knivd/Configum1/graphics/3D-BOTTOM.JPG

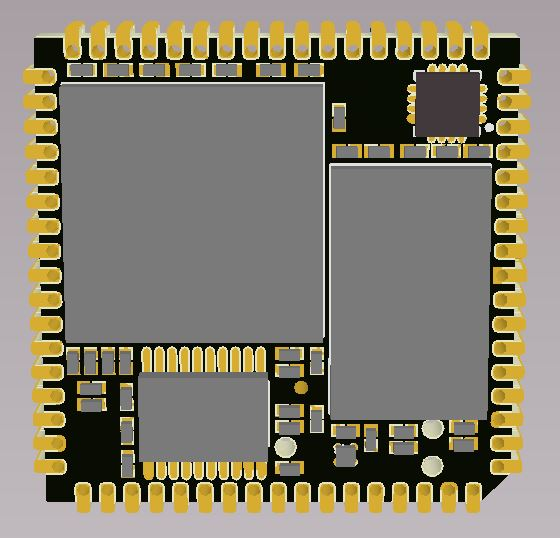
graphics/3D-BOTTOM.JPG
