knivd/Configum1/graphics/3D-TOP.JPG

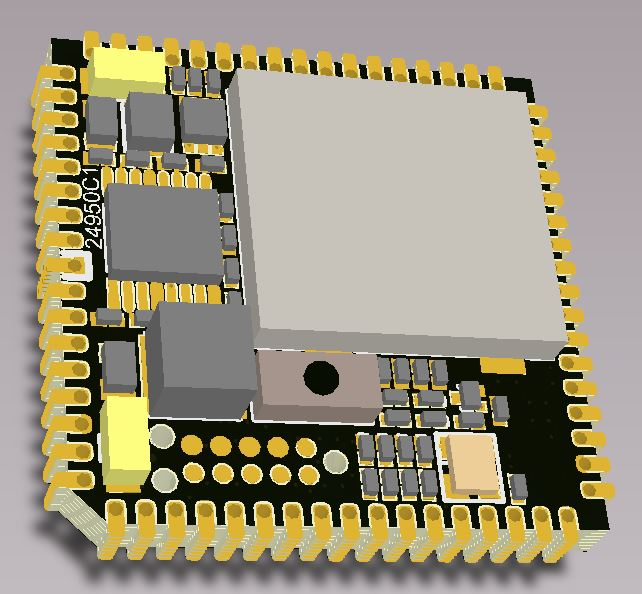
graphics/3D-TOP.JPG
