knivd/Configum1/graphics/DTX2-4950C.jpg

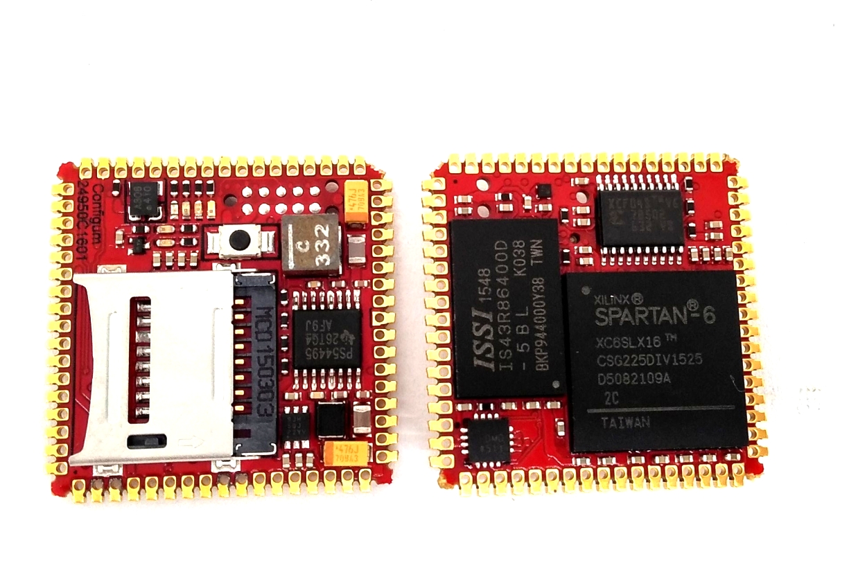
graphics/DTX2-4950C.jpg
