knivd/Configum1/docs/Spartan 6/Examples/BPC3010_Papilio_Pro.pdf

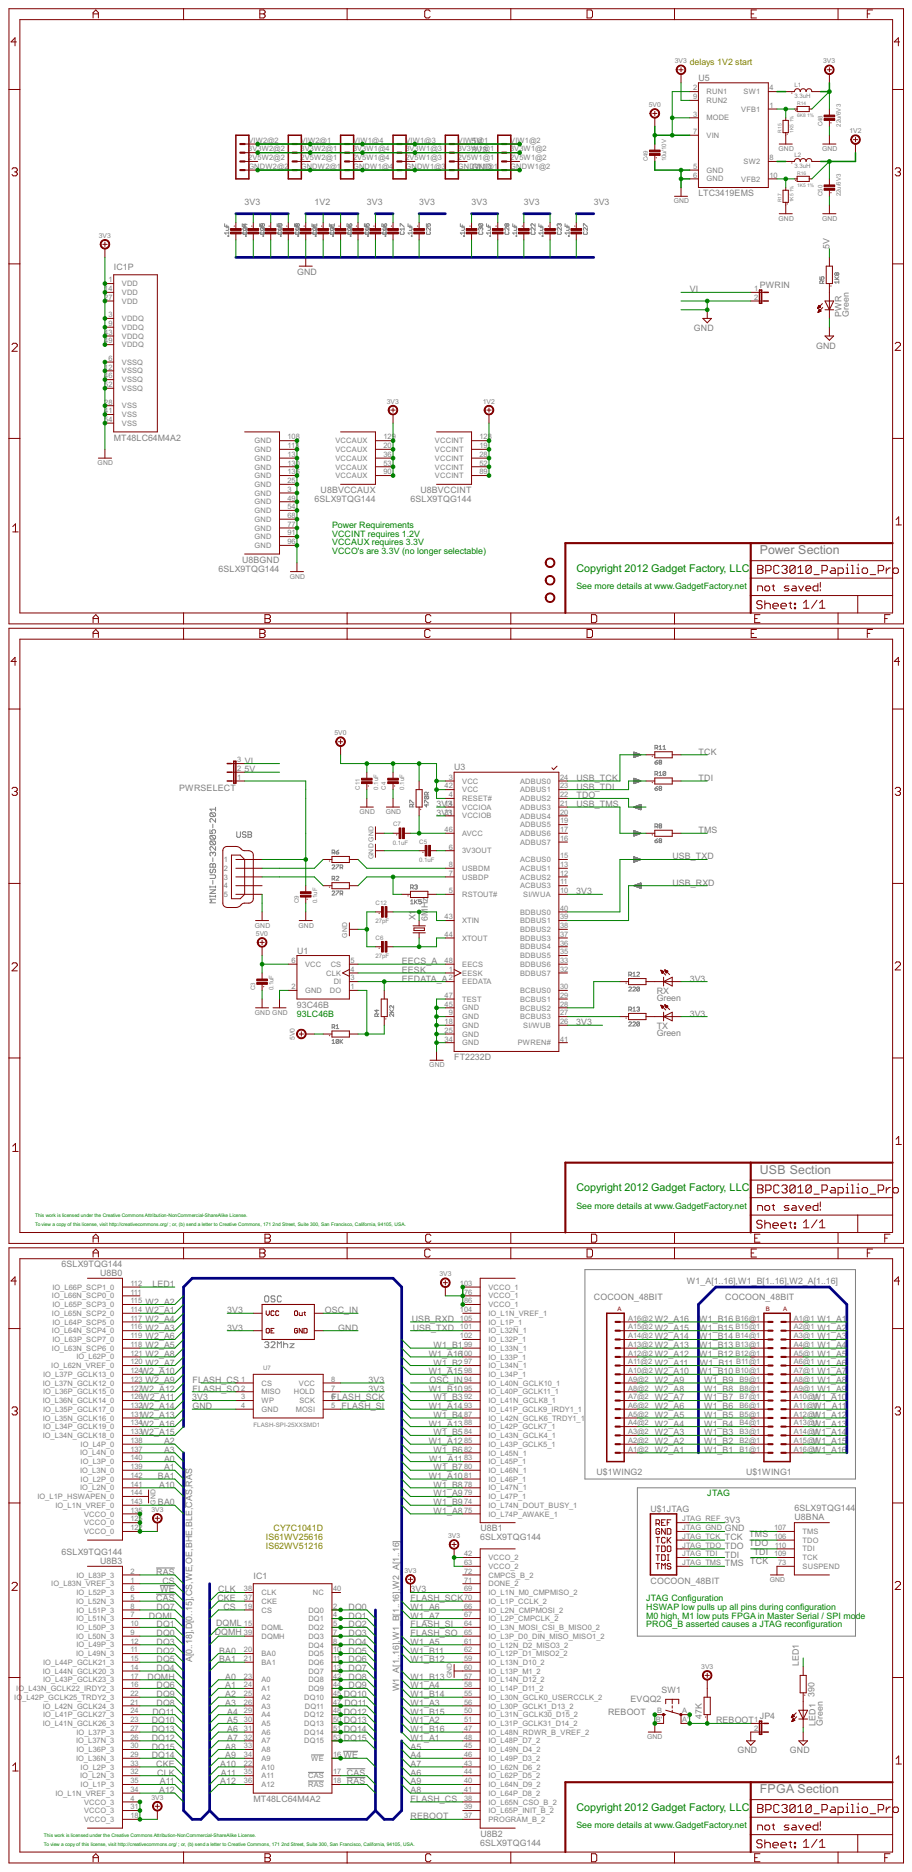
[picture p12: page 1]

3V3W2@2 VIW2@2 GNDW2@2 | 3V3W2@1 VIW2@1 GNDW2@1 | 3V3W1@4 VIW1@4 GNDW1@4 | 3V3W1@3 VIW1@3 GNDW1@3 | 3V3W1@1 VIW1@1 GNDW1@1 3V3

2V5W2@2 | 2V5W2@1 | 2V5W1@4 | 2V5W1@3 | 2V5W1@1 GND

Power Requirements VCCINT requires 1.2V

VCCAUX requires 3.3V
VCCO's are 3.3V (no longer selectable)

Copyright 2012 Gadget Factory, LLC

See more details at www.GadgetFactory.net

A[0..18],D[0..15],CS,WE,OE,BHE,BLE,CAS,RAS

JTAG Configuration HSWAP low pulls up all pins during configuration M0 high, M1 low puts FPGA in Master Serial / SPI mode PROG_B asserted causes a JTAG reconfiguration

This work is licensed under the Creative Commons Attribution-NonCommercial-ShareAlike License. To view a copy of this license, visit http://creativecommons.org/ ; or, (b) send a letter to Creative Commons, 171 2nd Street, Suite 300, San Francisco, California, 94105, USA.
