knivd/Configum1/docs/Spartan 6/Examples/SCH-TE0600-02.pdf

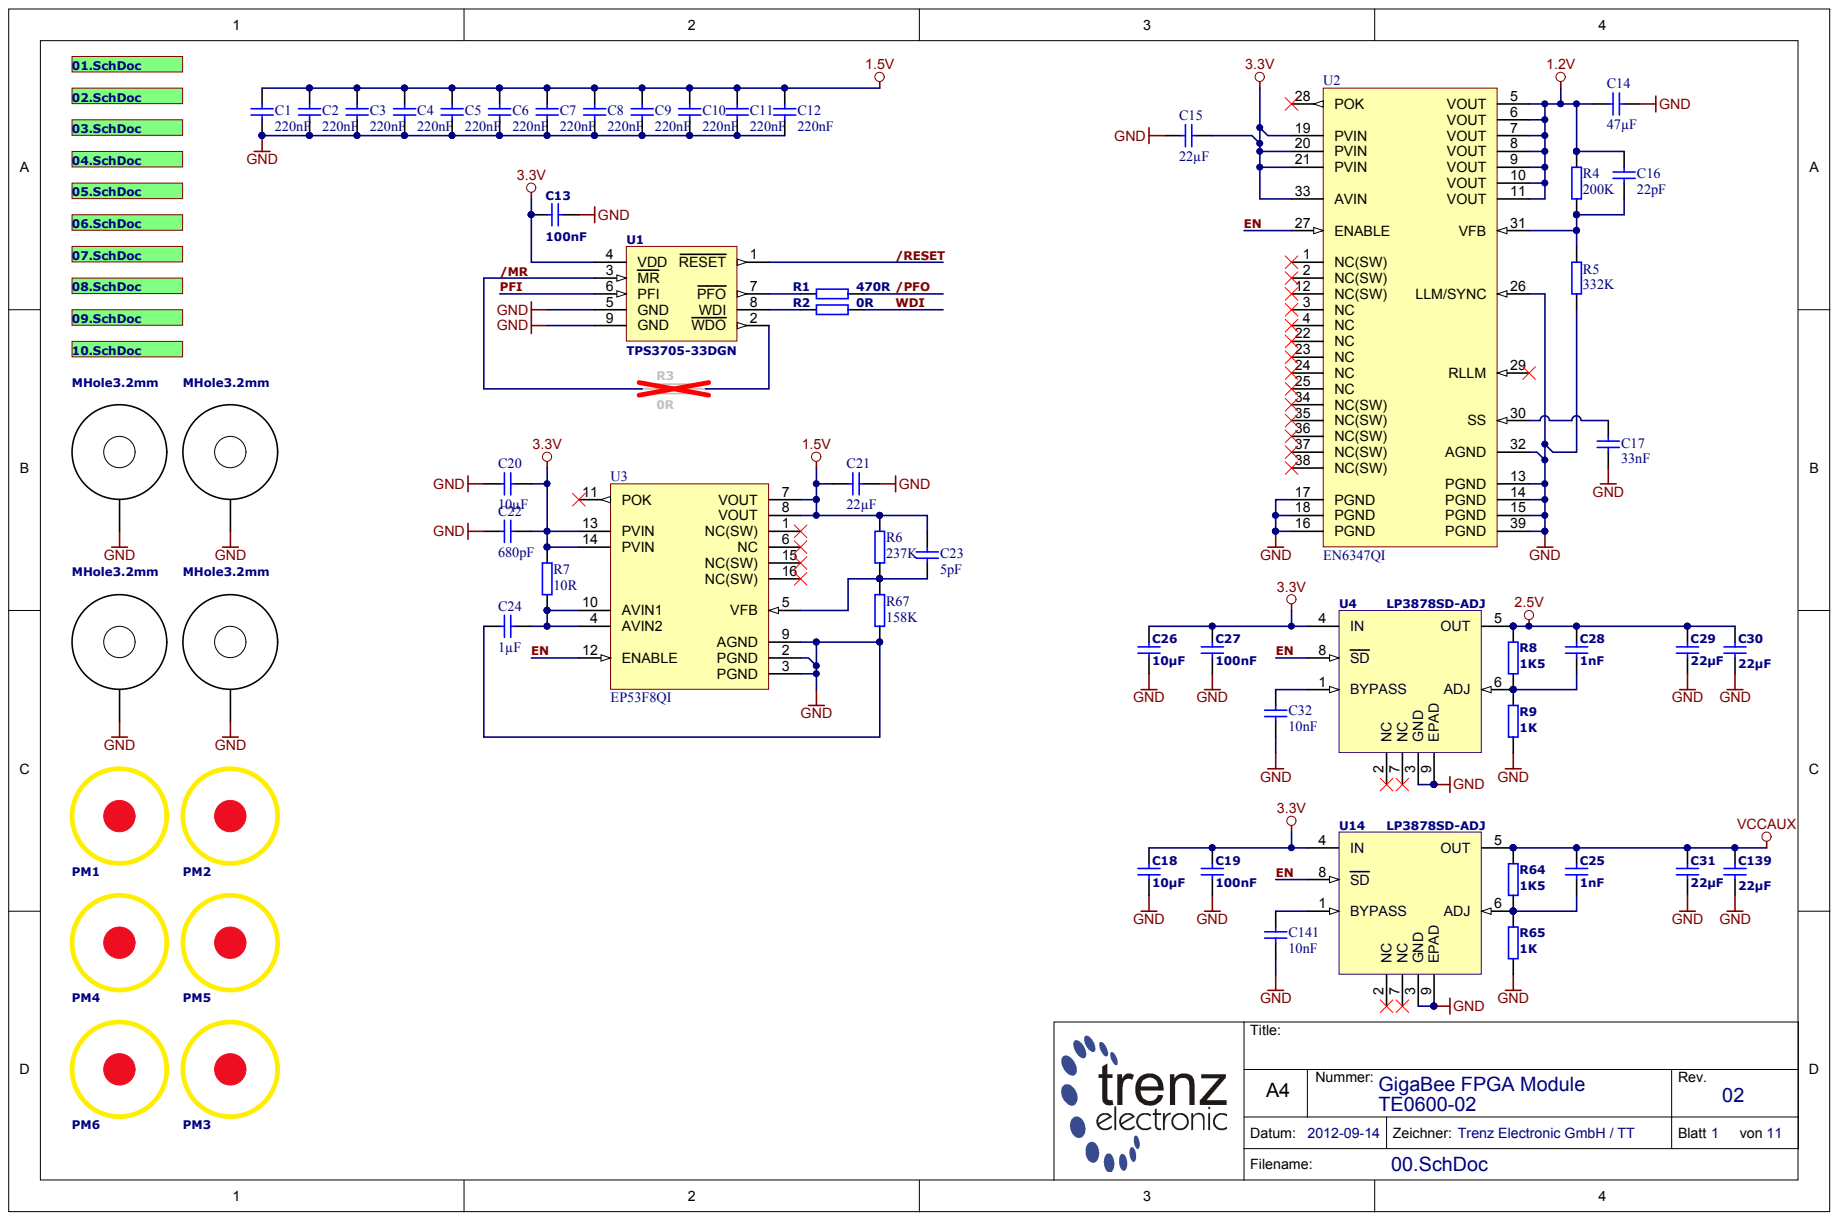
[picture p13: page 1]

Title:

A4 | Nummer: GigaBee FPGA Module | Rev. 02

Datum: | Zeichner: Trenz Electronic GmbH / TT | Blatt 1 von 11

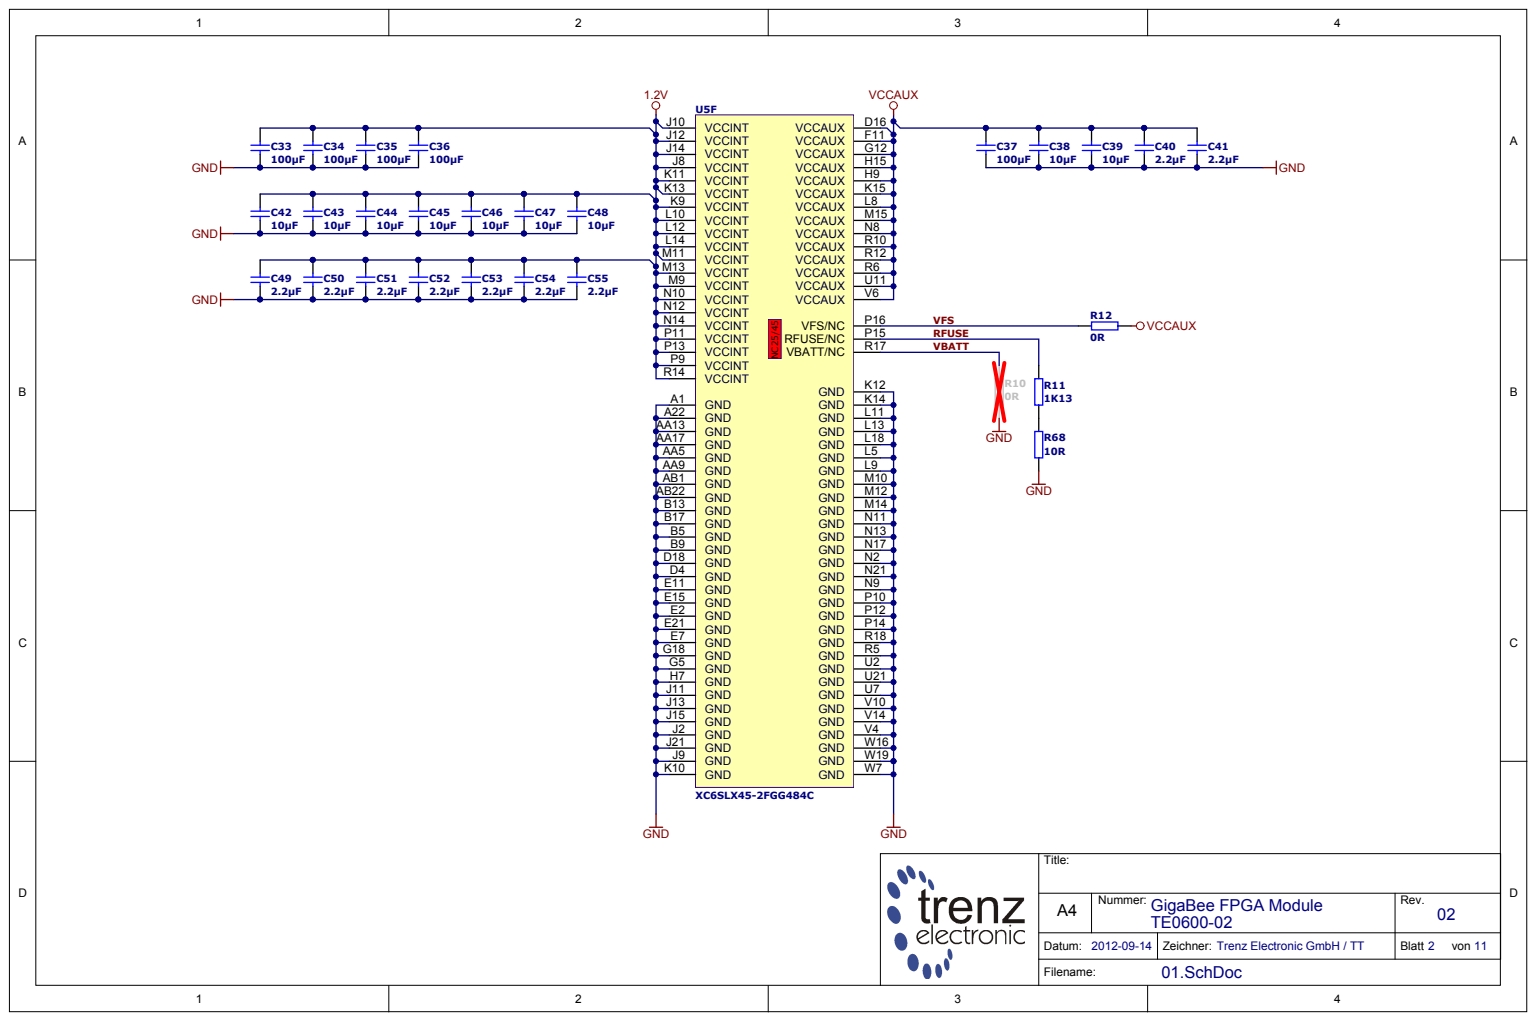
[picture p14: page 2]

VCCINT J14
VCCINT J8
VCCINT K11
VCCINT K13

VCCINT L10
VCCINT L12
VCCINT L14
VCCINT M11

VCCINT M9
VCCINT N10
VCCINT N12
VCCINT N14
VCCINT P11

GND A22
GND AA13
GND AA17
GND AA5
GND AA9
GND AB1
GND AB22
GND B13
GND B17
GND B5
GND B9
GND D18
GND D4
GND E11
GND E15
GND E2
GND E21
GND E7
GND G18
GND G5
GND H7
GND J11
GND J13
GND J15
GND J2
GND J21
GND J9

Title:

A4 | Nummer: GigaBee FPGA Module | Rev. 02

Datum: | Zeichner: Trenz Electronic GmbH / TT | Blatt 2 von 11

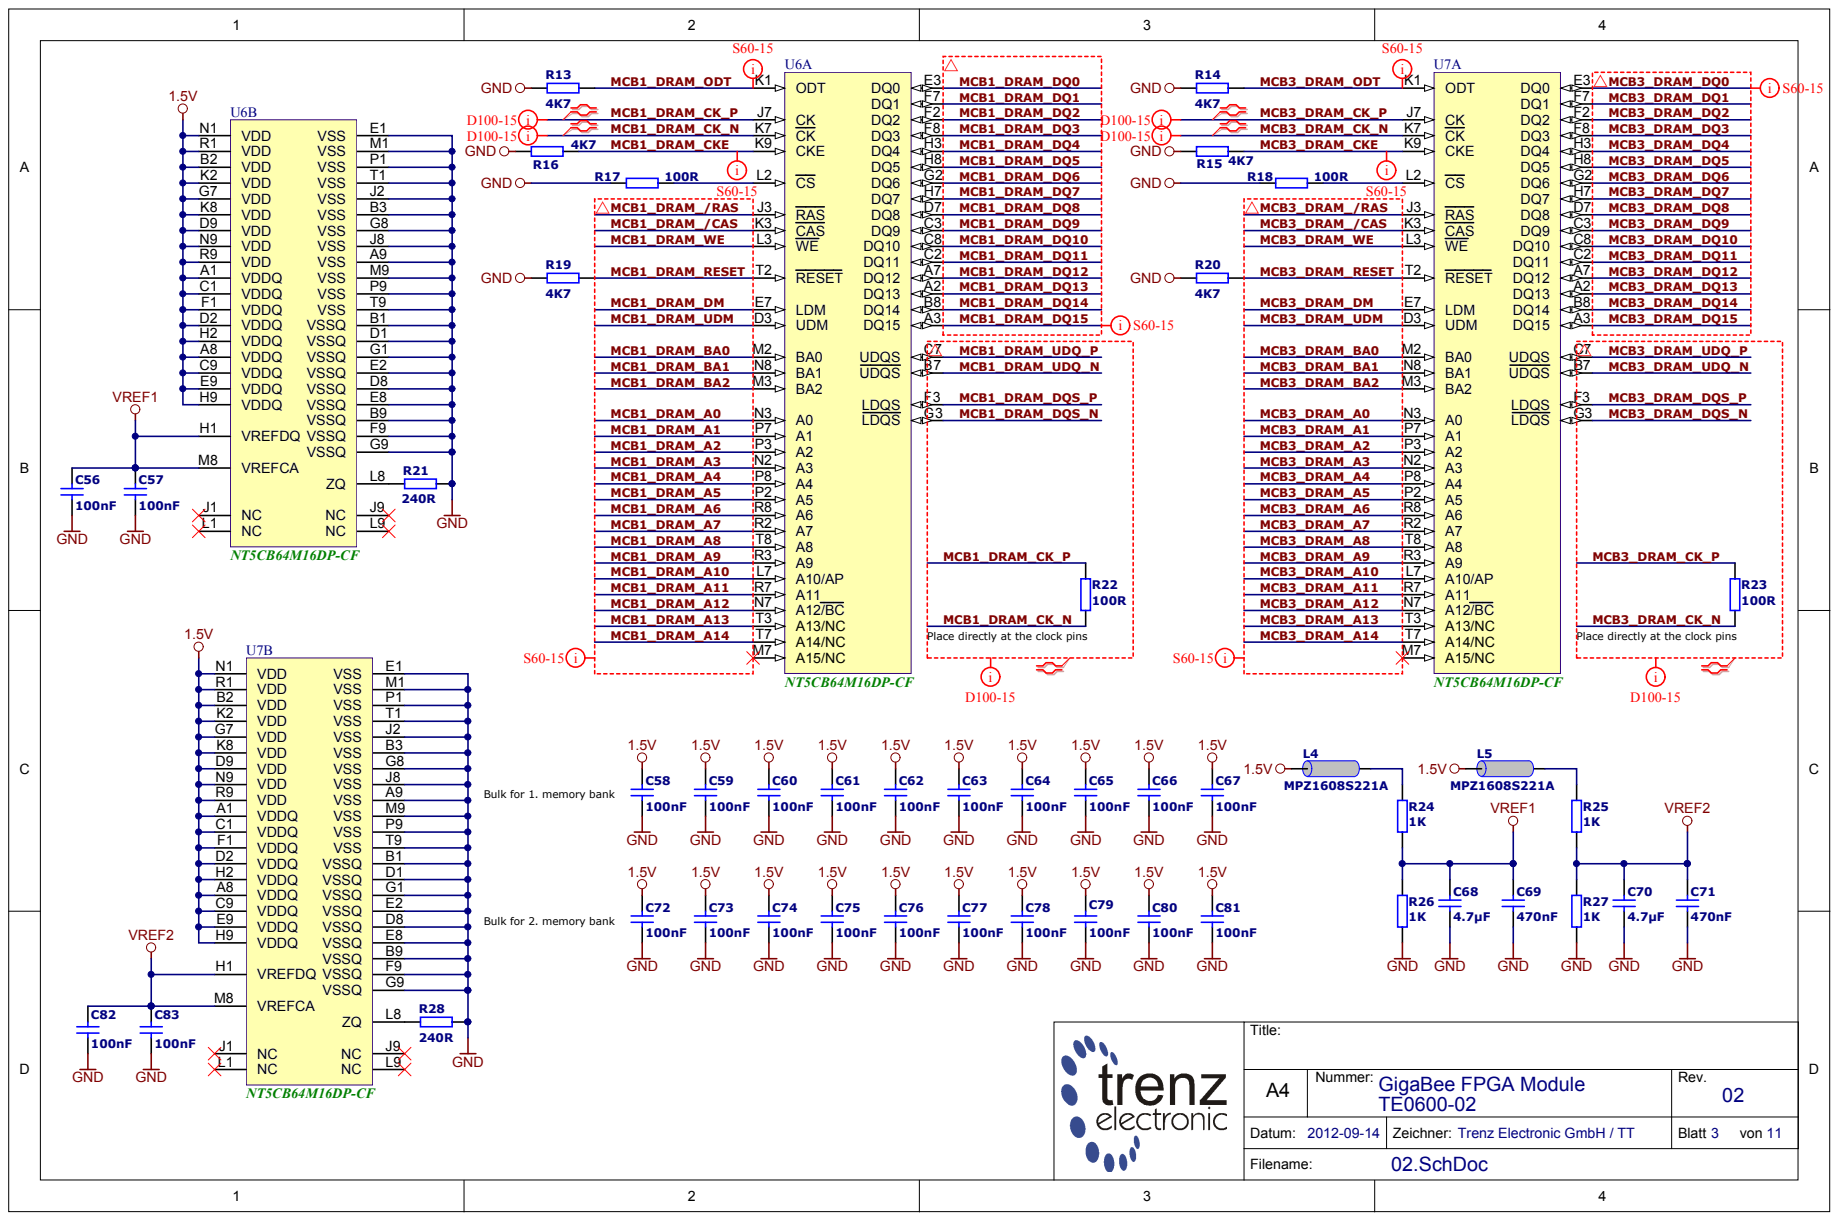
[picture p15: page 3]

VDD R1
VDD B2
VDD K2
VDD G7
VDD K8
VDD D9
VDD N9
VDD R9

Bulk for 1. memory bank

VDDQ A1
VDDQ C1
VDDQ F1
VDDQ D2
VDDQ H2
VDDQ A8
VDDQ C9

Bulk for 2. memory bank

Title:

A4 | Nummer: GigaBee FPGA Module TE0600-02 | Rev. 02

Datum: 2012-09-14 | Zeichner: Trenz Electronic GmbH / TT | Blatt 3 von 11

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
D | D
C | C
B | B
A | A
| Title:
A4 | Nummer: GigaBee FPGA Module TE0600-02 | Rev. 02
Datum: 2012-09-14 | Zeichner: Trenz Electronic GmbH / TT | Blatt 4 von 11
Filename: | 03.SchDoc

Trace widths should be 3 to 5 mils.
? | Trace spacing should be three times the trace width.
? | Signals must not be routed over splits or voids.
? | Routing of differential pairs adjacent to noisy signal lines or high-speed
switching
devices such as clock chips should be avoided.
? The spacing between differential clocks/strobes and other signals on the same PCB
layer should be 20 mil. The 20 mil spacing should be maintained when using serpentine routing for length matching.
Differential clocks/strobes are to be routed as 100O differential signals. The clock
pairs must be routed on the same PCB layer with no layer changes or hops after the
initial pad to via breakout.
The Data (DQ), Data Mask (DM), and Data Strobe (DQS) signals should receive the highest
priority (that is, routed first), because they are the highest speed DDR signals. ? DQ, DM, and DQS signals should be routed in a data group (per byte). Each group should have similar loading and routing to maintain timing and signal integrity. ? The provided spacing should be 20 mil between a data group and any other signals.
? | DQS signals should be isolated from other signals by 20 mil to avoid crosstalk.
? | There should be a maximum of ±25 ps electrical delay (±150 mil) between any
DQ/DM and its associated DQS strobe.
? | A data group should be referenced to a GROUND plane.
? | DQ bit swapping at the memory interface is permitted to facilitate layout.
Swapping
should only be done within a data group.
? | DQS to DQS_N trace lengths should be matched (±10 mil).
? | Memory terminations (if external terminations are used) should be placed after
the
associated memory component in a fly-by fashion.
? For 16-bit DDR devices, the LDQS/LDQS_N and UDQS/UDQS_N trace lengths
should be matched within ±25 ps of the electrical delay (±150 mil).
When the data groups have been routed, the next highest priority is the differential clock
(CK / CK_N). The clock should be routed first because all address and control trace length
matching must be referenced to the differential clock PCB trace length, which might need
to be adjusted as the layout task proceeds.
? | CK to CK_N trace lengths must be matched (±10 mil).
? | CK and DQS trace lengths must be matched (±250 mil) to maximize setup and hold
margins.
? There must be a maximum ±50 ps electrical delay (±300 mil) between any address/control signals and the associated CK and CK_N differential clock FPGA output.
? Address and control signals can be referenced to a POWER plane if a GROUND plane
is not next to this group of signals in the PCB stack-up.
To avoid crosstalk, address and command signals should be kept on a different routing layer from DQ, DQS, and DM.
? Differential clock terminations (if external terminations are used) must be located as
close as possible to the load, after the clock pads of the PCB. PCB trace lengths used in
trace length matching must exclude the CLINE length of the PCB trace from memory ball to terminating resistor.

Classnames:
S60-15 uses 1.5V or GND plane as reference D100-15 uses 1.5V or GND plane as reference

S60-25 uses 2.5V or GND plane as reference D100-25 uses 2.5V or GND plane as reference

S60-IO uses VCCIO0 or GND plane as reference D100-IO uses VCCIO0 or GND plane as reference

S60-33 uses 3.3V or GND plane as reference D100-33 uses 3.3V or GND plane as reference

R74 | 0R
R76 | 0R
R77 | 0R
GND R78 | 0R

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
Board Revisions

Assembly Variants

Enable pullups in FPGA

AV0 = 0 -> commercial AV0 = 1 -> Industrial

AV3 AV2 AV1
0 | 0 | 0 | 2 x 128 MBit, speedgrade 2
0 | 0 | 1 | 2 x 128 MBit, speedgrade 3
0 | 1 | 0 | 2 x 512 MBit, speedgrade 3

BR3 BR2 BR1 BR0
1 | 1 | 1 | 1 | -01 Initial revision
1 | 1 | 1 | 0 | -02 | GND

### NetTie1

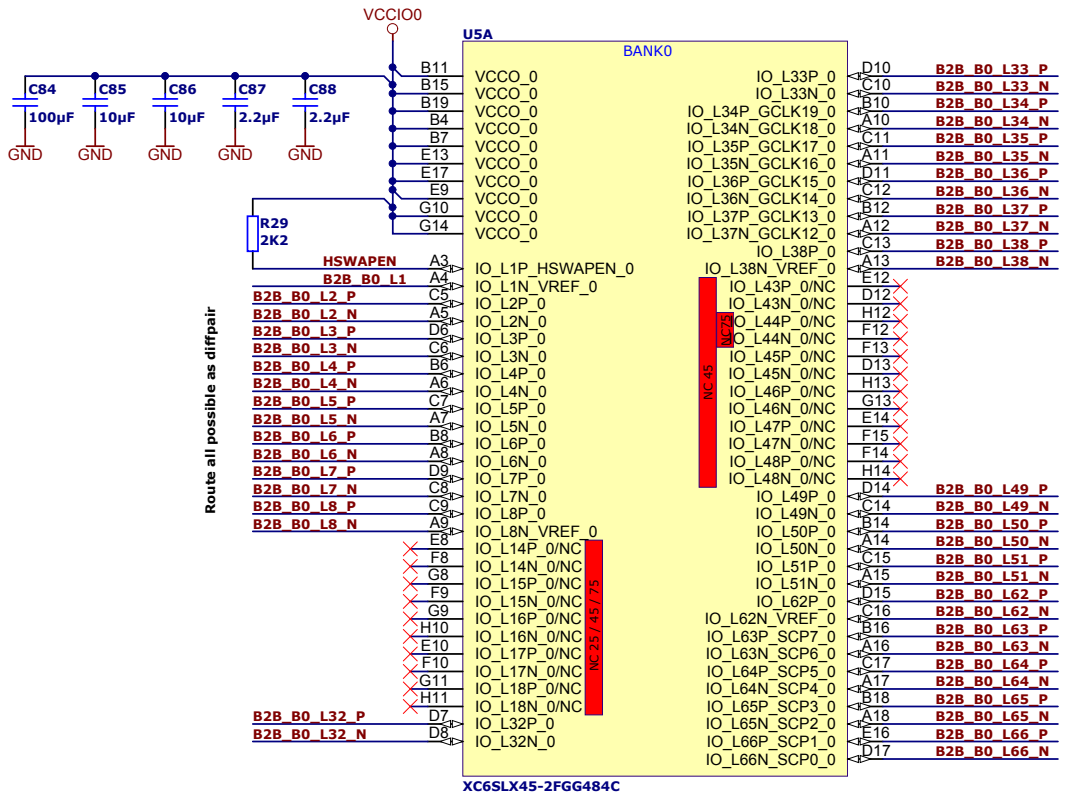
[picture p16: page 5]

VCCO_0 B19
VCCO_0 B4
VCCO_0 B7
VCCO_0 E13
VCCO_0 E17

Title:

A4 | Nummer: GigaBee FPGA Module | Rev. 02

Datum: | Zeichner: Trenz Electronic GmbH / TT | Blatt 5 von 11

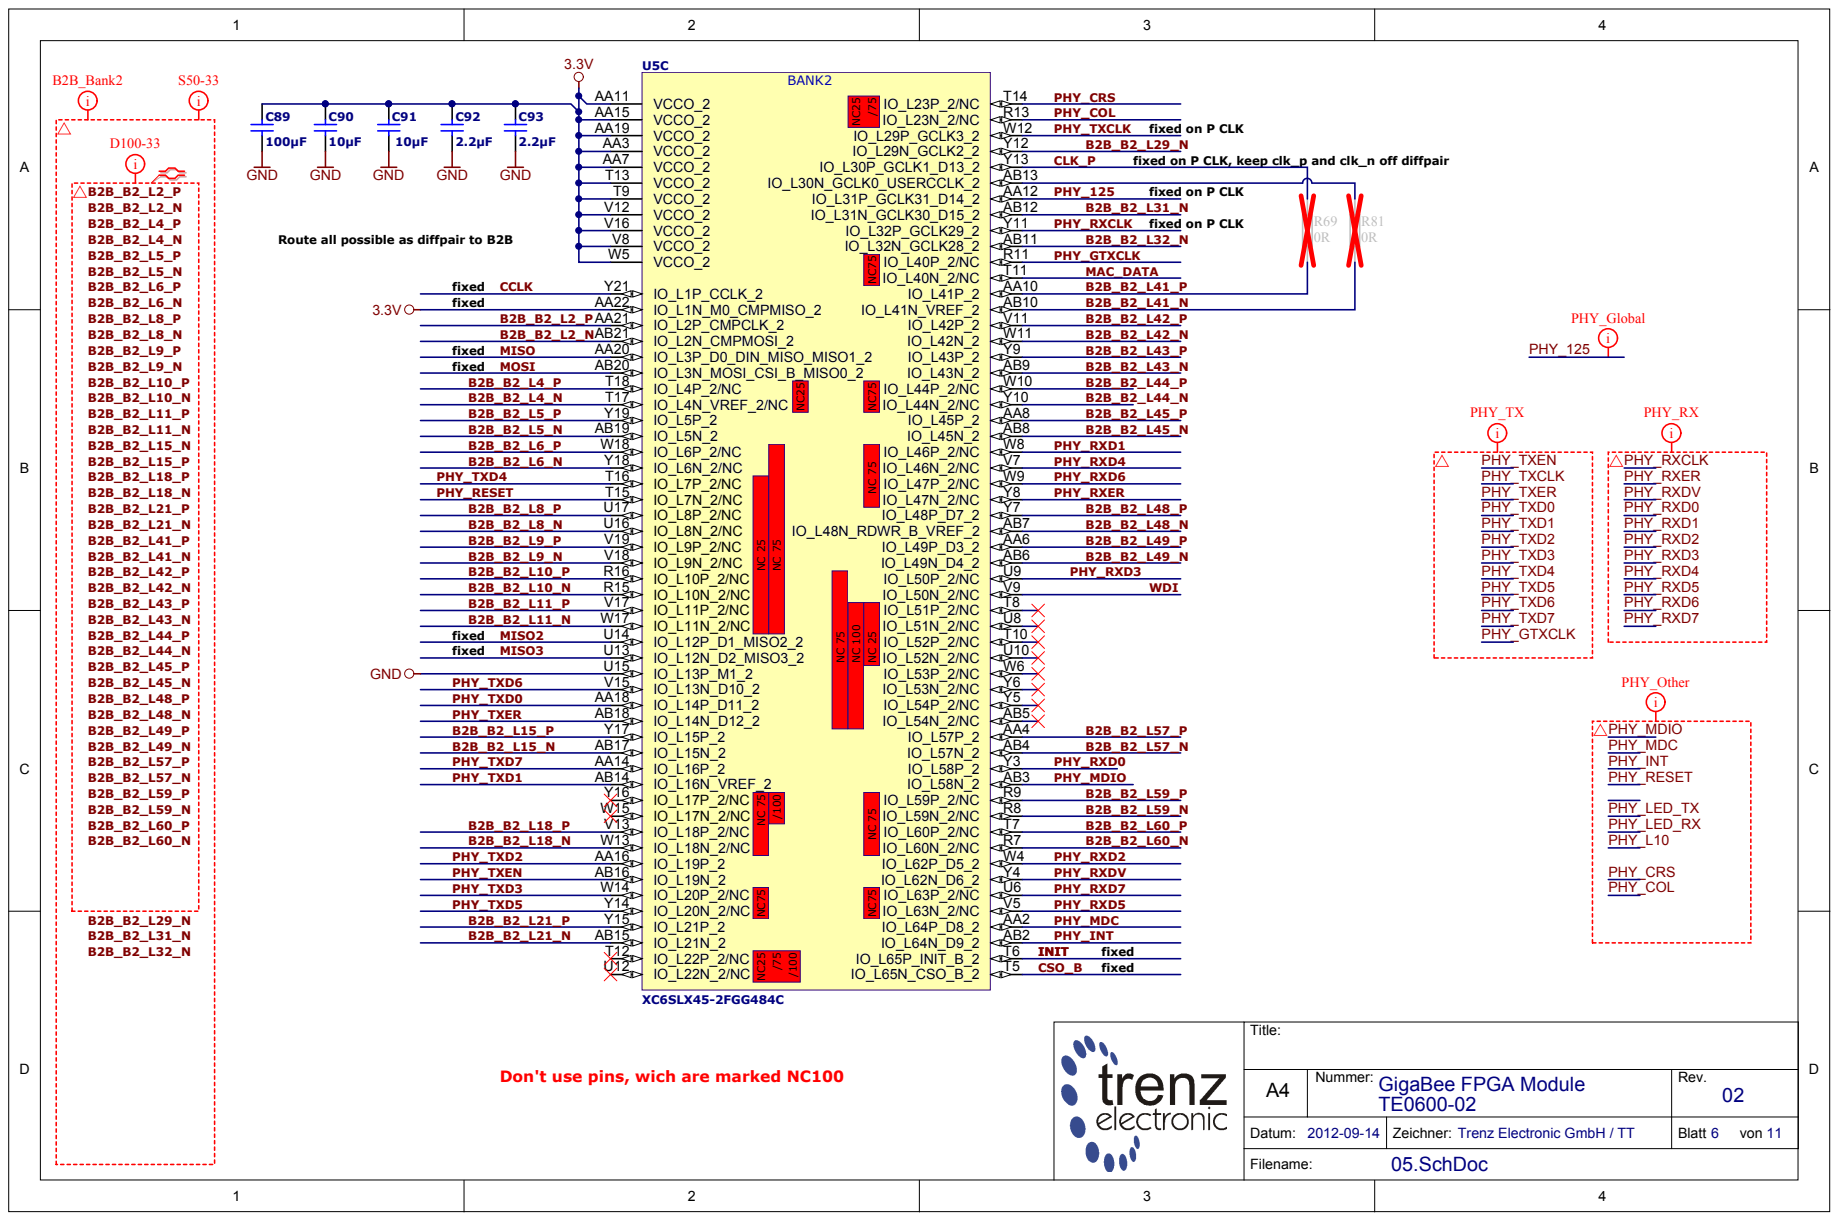
[picture p17: page 6]

VCCO_2 AA3
VCCO_2 AA7

K, keep clk_p and clk_n off diffpair

VCCO_2 T9 | PHY_125 fixed on P C L K
VCCO_2 V12
VCCO_2 V16
VCCO_2 V8

sible as diffpair to B2B

Title:

Don't use pins, wich are marked NC100

A4 | Nummer: GigaBee FPGA Module | Rev. 02

Datum: | Zeichner: Trenz Electronic GmbH / TT | Blatt 6 von 11

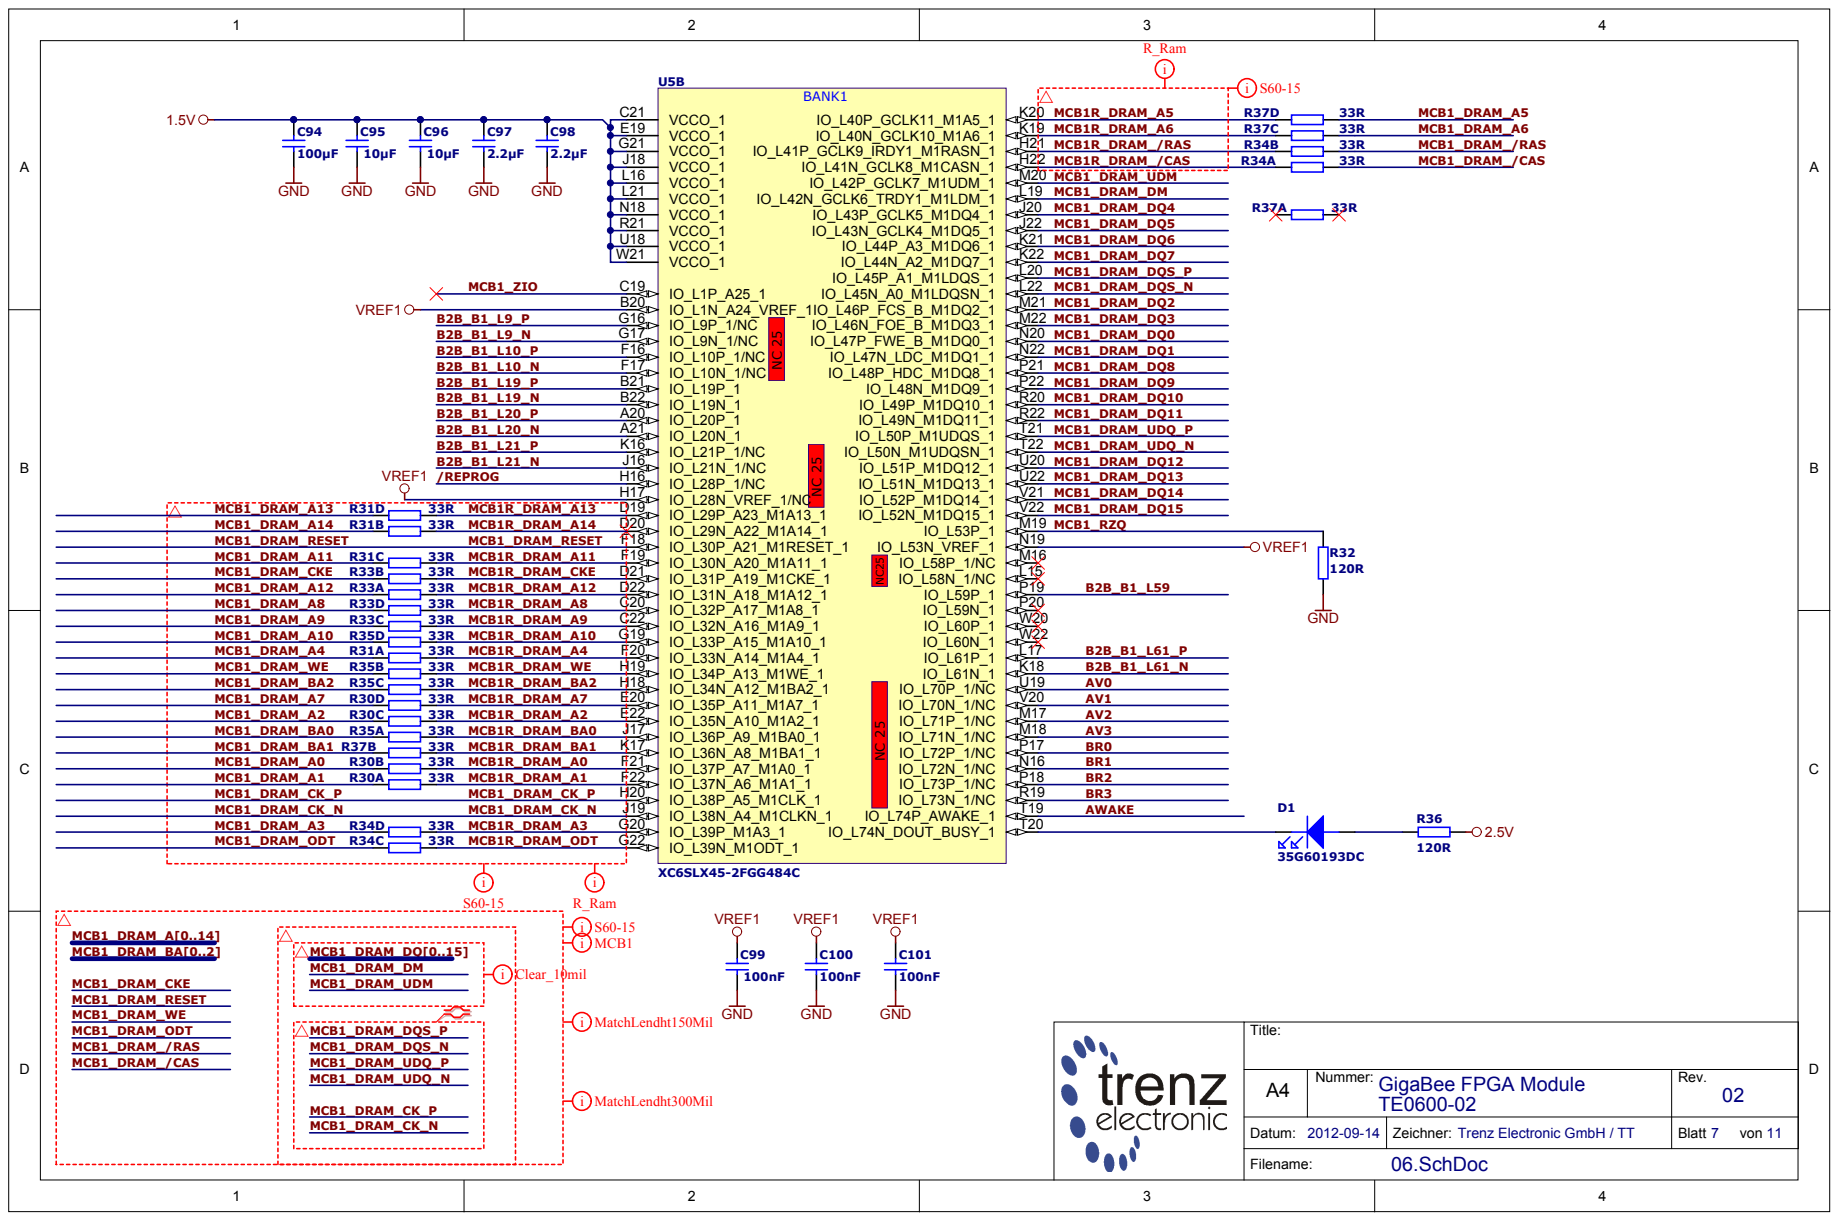
[picture p18: page 7]

VCCO_1 E19 | M CB1R_DRAM_A6
VCCO_1 G21 | M CB1R_DRAM_/RAS
VCCO_1 J18 | M CB1R_DRAM_/CAS
VCCO_1 L16
VCCO_1 L21
VCCO_1 N18
VCCO_1 R21
VCCO_1 U18

M CB1_DRAM_RESE T | IO_L30P_A21_M1RESET_1 F18

M CB1_DRAM_C K_P | IO_L38P_A5_M1CLK_1 H20
M CB1_DRAM_C K_N | IO_L38N_A4_M1CLKN_1 J19

A4 | Nummer: GigaBee FPGA Module | Rev. 02

Datum: | Zeichner: Trenz Electronic GmbH / TT | Blatt 7 von 11

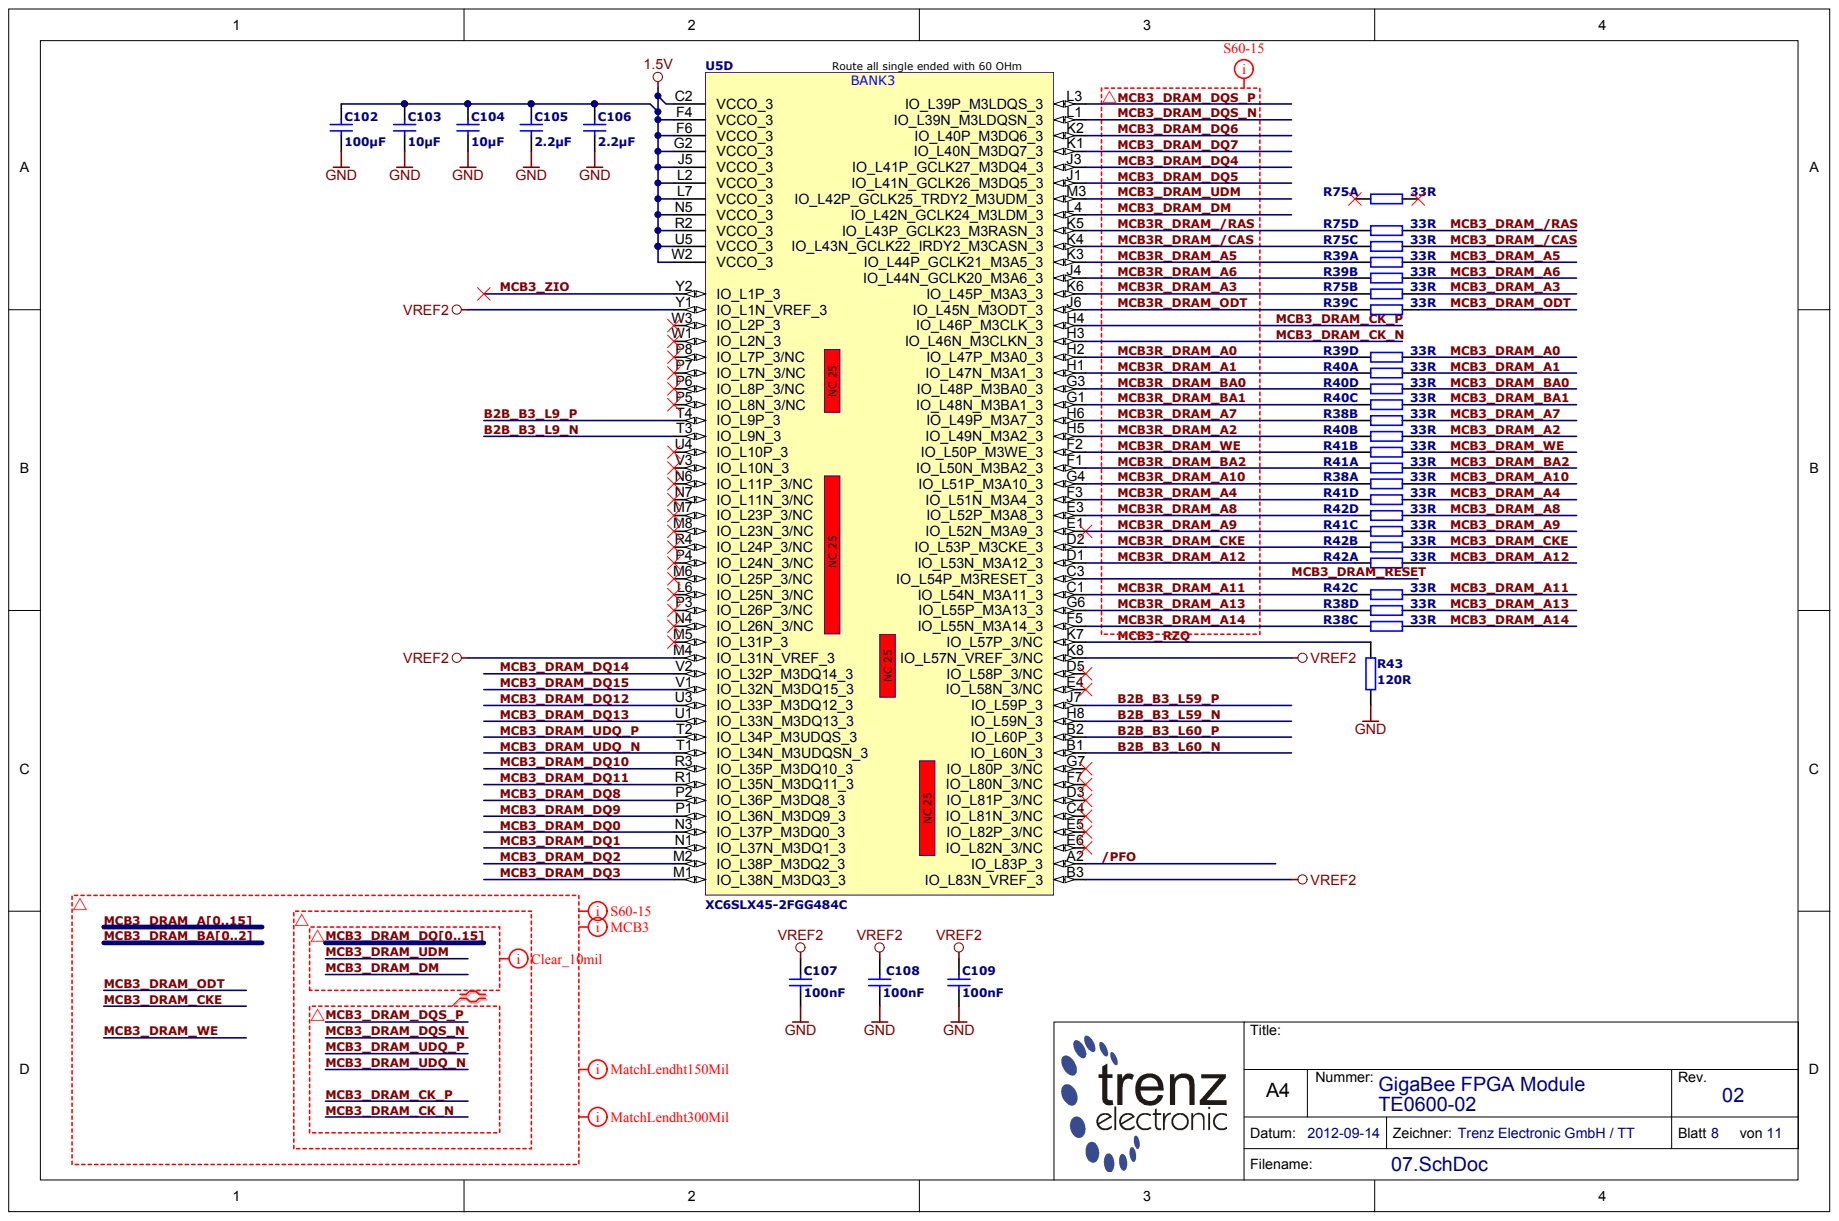
[picture p19: page 8]

Route all single ended with 6
BANK3

VCCO_3 F6
VCCO_3 G2
VCCO_3 J5
VCCO_3 L2
VCCO_3 L7
VCCO_3 N5
VCCO_3 R2
VCCO_3 U5 | M CB3R_DRAM_/CAS
VCCO_3 W2 | M CB3R_DRAM_A5
IO_L1P_3 Y2 IO_L1N_VREF_3 Y1 | M CB3R_DRAM_A6

M CB3R_DRAM_A3
M CB3R_DRAM_ODT

IO_L2P_3 W3 | M CB3R_DRAM_A0

IO_L9P_3 T4 IO_L9N_3 T3 IO_L10P_3 U4 | M CB3R_DRAM_A7

M CB3R_DRAM_A2
M CB3R_DRAM_W E

IO_L10N_3 V3 | M CB3R_DRAM_BA2
IO_L11P_3/NC N6 | M CB3R_DRAM_A10

Title:

A4 | Nummer: GigaBee FPGA Module | Rev. 02

Datum: | Zeichner: Trenz Electronic GmbH / TT | Blatt 8 von 11

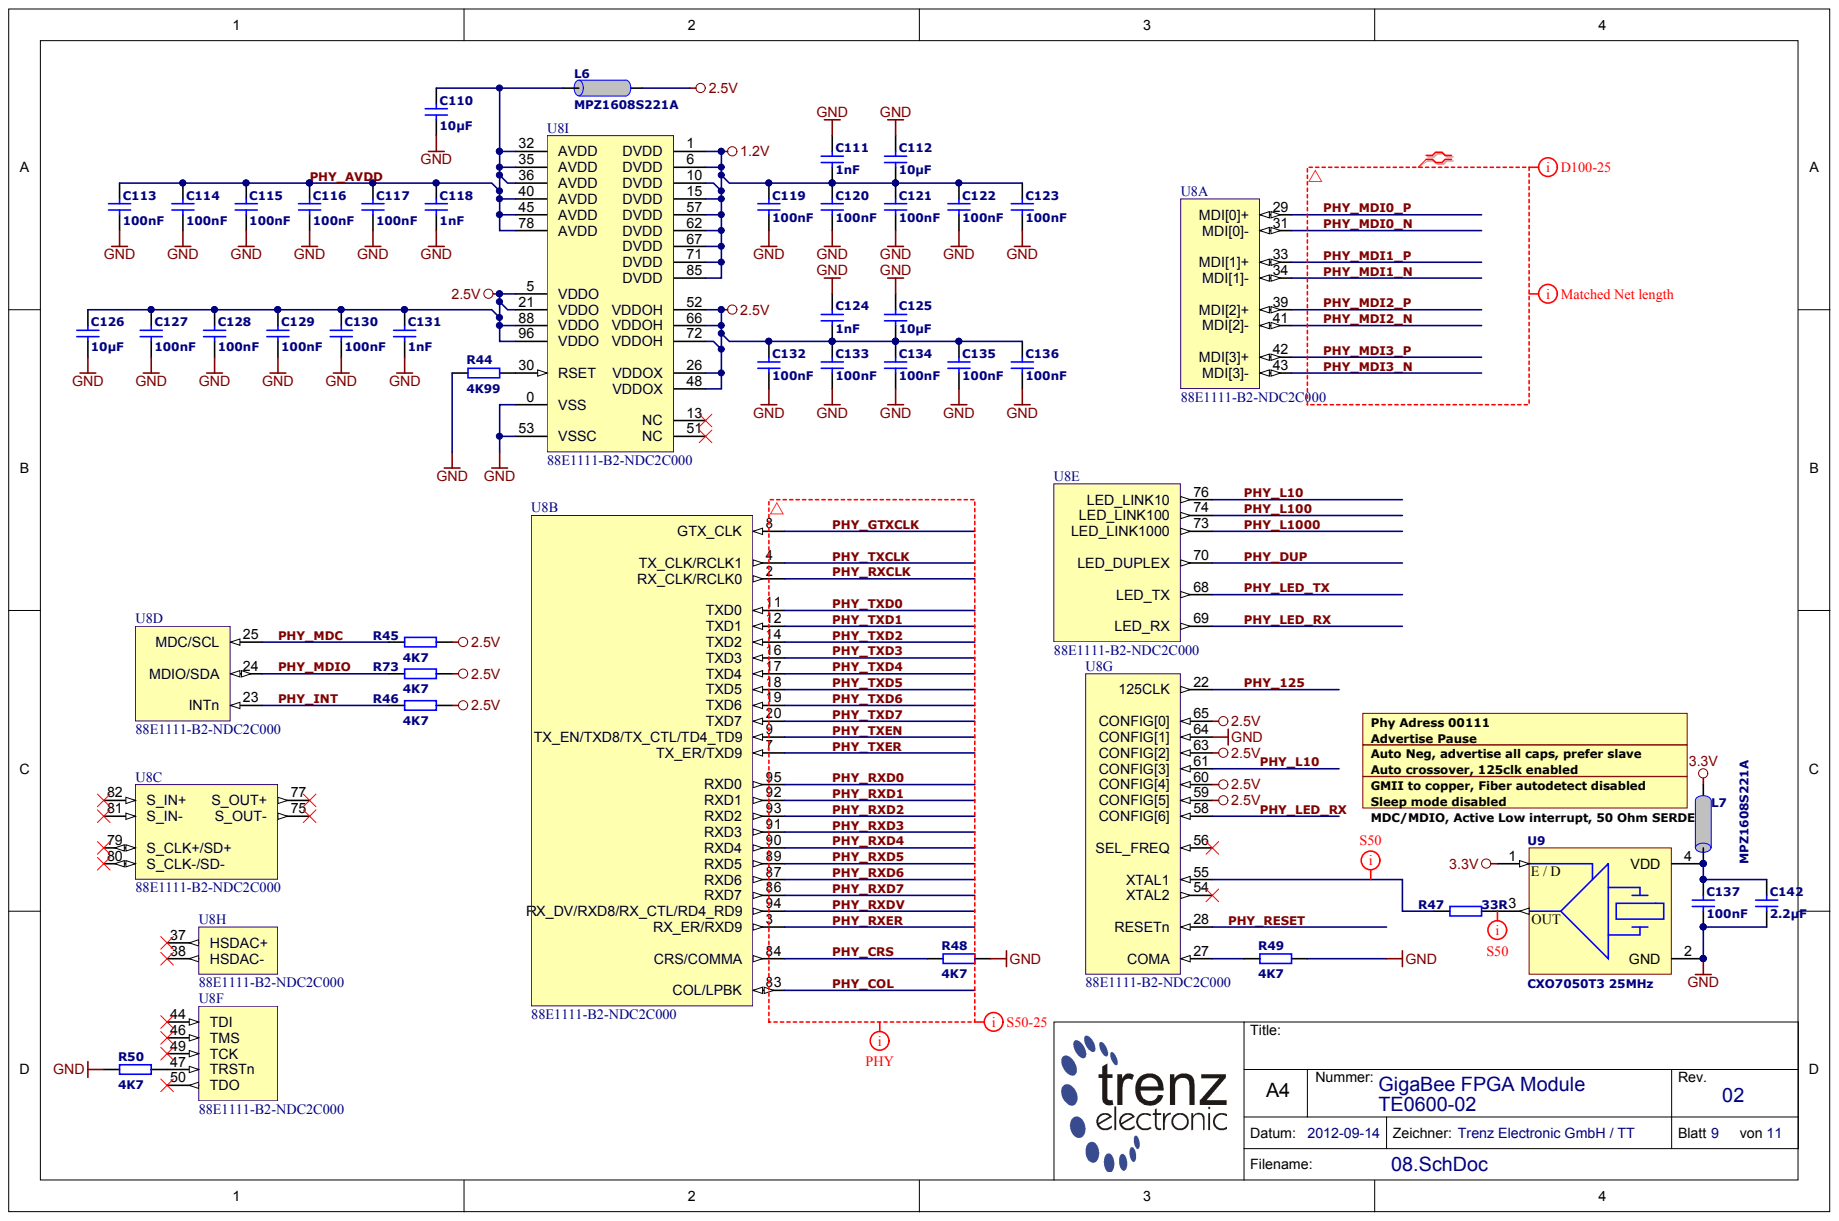
[picture p20: page 9]

PHY_TXCLK
PHY_RXCLK

PHY_TXD0
PHY_TXD1
PHY_TXD2
PHY_TXD3
PHY_TXD4

PHY_TXD6
PHY_TXD7
PHY_TXEN

Auto Neg, advertise all caps, prefer slave
Auto crossover, 125clk enabled
GMII to copper, Fiber autodetect disabled
Sleep mode disabled

PHY_RXD3
PHY_RXD4
PHY_RXD5
PHY_RXD6

Zeichner: Trenz Electronic GmbH / TT

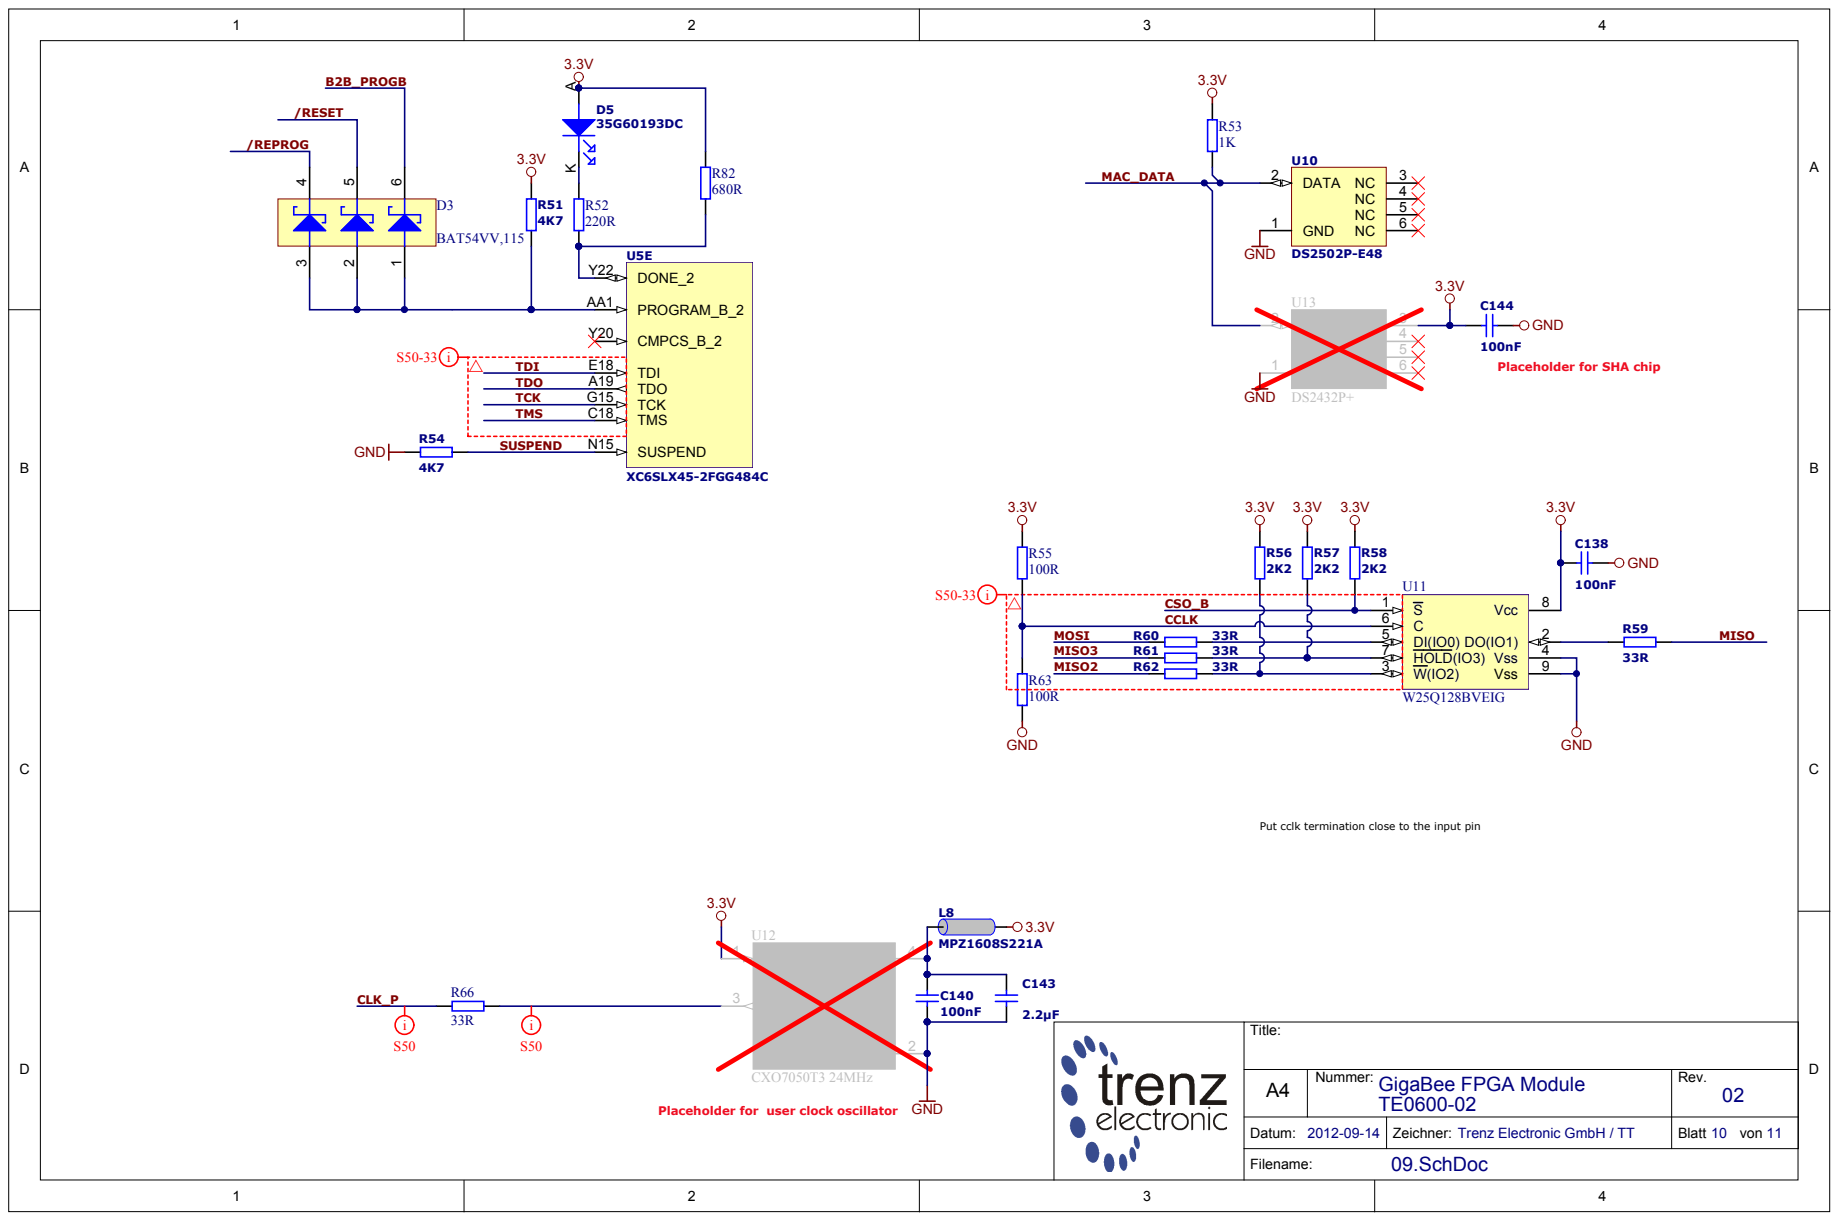
[picture p21: page 10]

Placeholder for SHA chip

Put cclk termination close to the input pin

Title:

A4 | Nummer: GigaBee FPGA Module TE0600-02 | Rev. 02

Placeholder for user clock oscillator

Datum: 2012-09-14 | Zeichner: Trenz Electronic GmbH / TT | Blatt 10 von 11

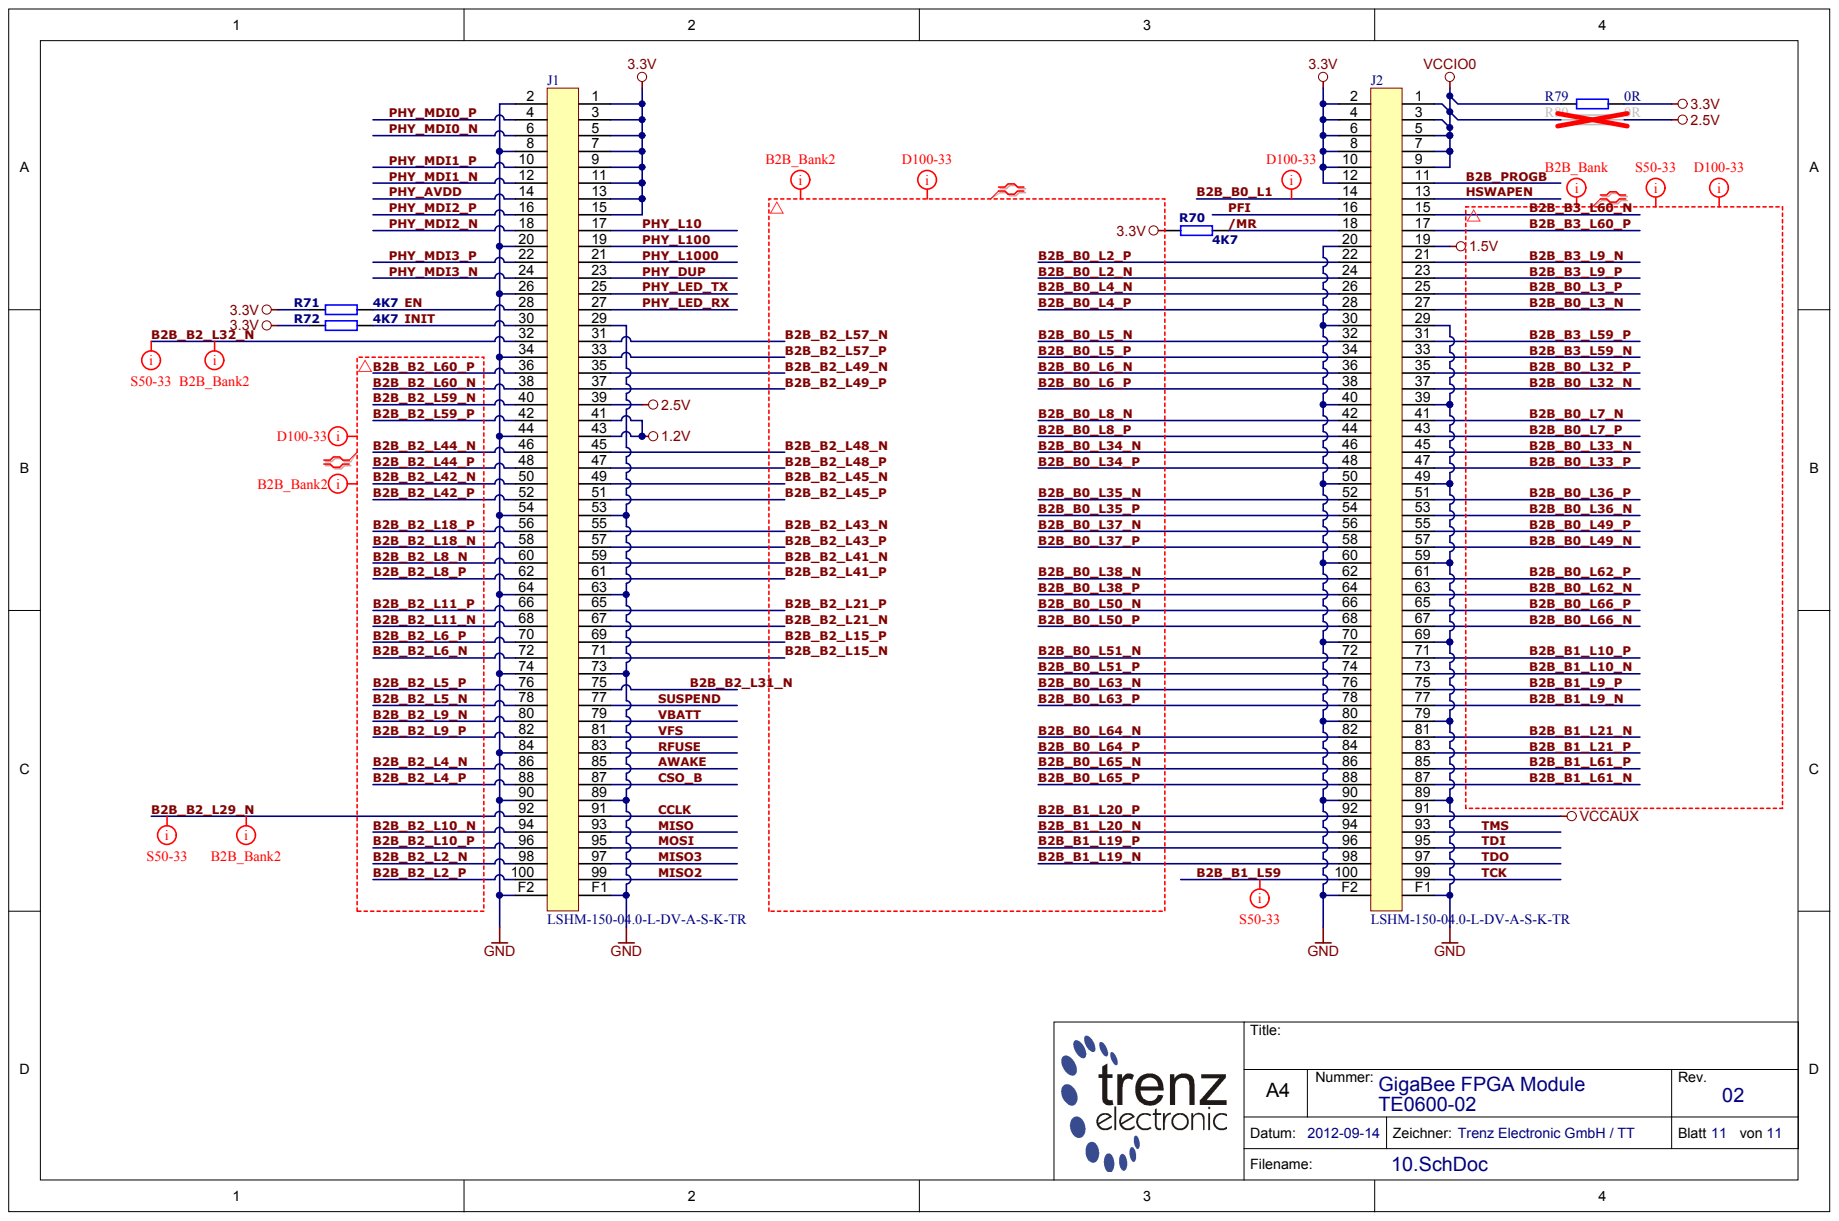
[picture p22: page 11]

12 | 11
14 | 13
16 | 15

Title:

A4 | Nummer: GigaBee FPGA Module | Rev. 02

Datum: | Zeichner: Trenz Electronic GmbH / TT | Blatt 11 von 11
