knivd/Configum1/docs/Spartan 6/Examples/SCH_MIXXEO.pdf

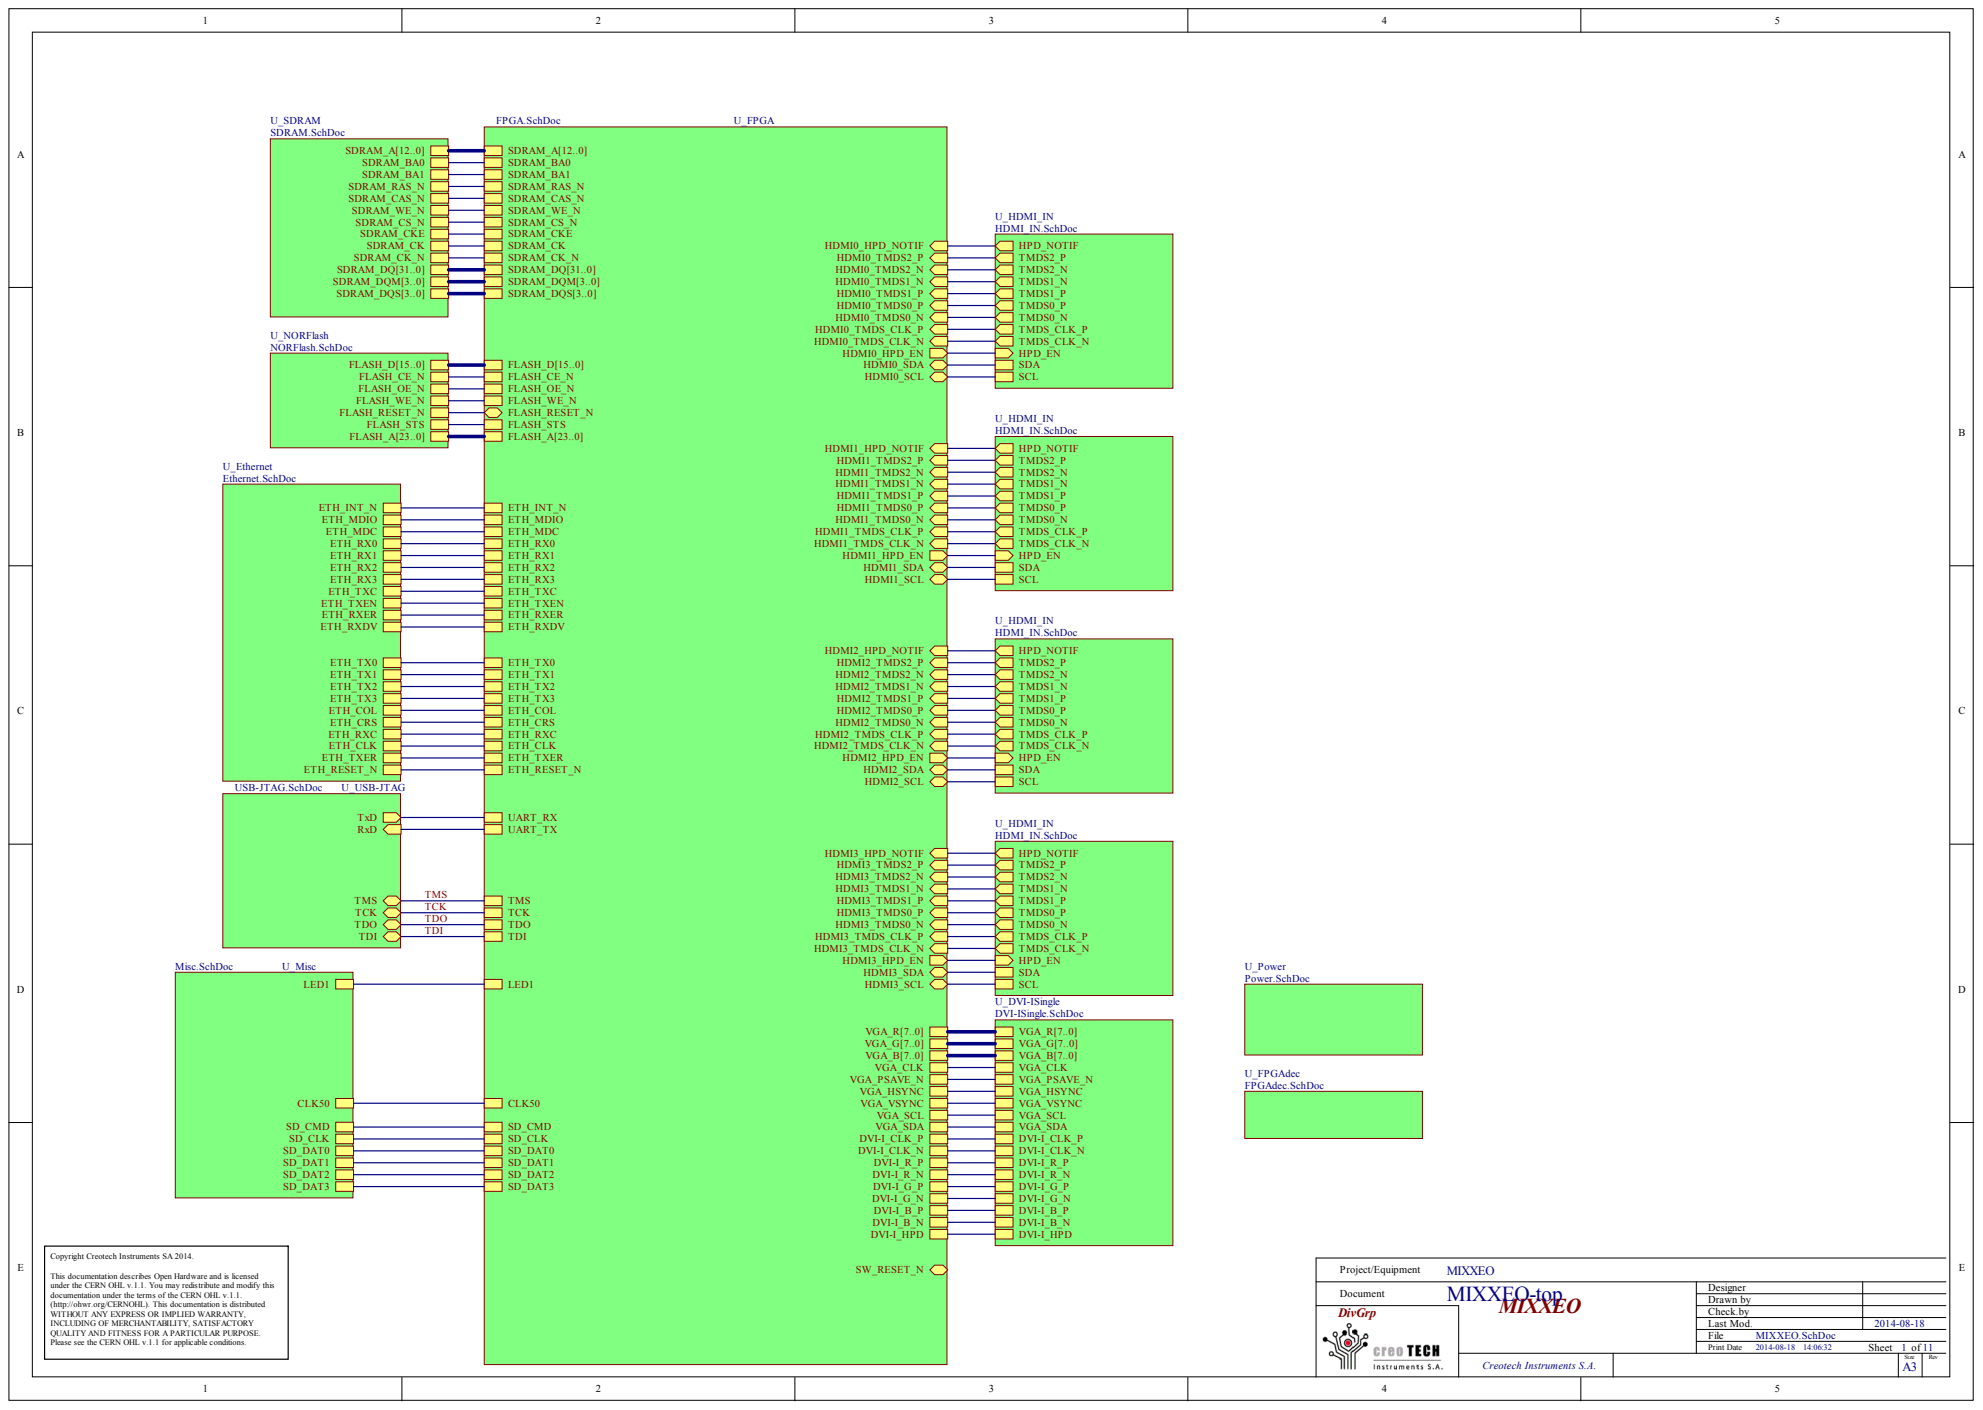
[picture p23: page 1]

Copyright Creotech Instruments SA 2014.

This documentation describes Open Hardware and is licensed
under the CERN OHL v.1.1. You may redistribute and modify this
documentation under the terms of the CERN OHL v.1.1.
(http://ohwr.org/CERNOHL). This documentation is distributed
WITHOUT ANY EXPRESS OR IMPLIED WARRANTY,
INCLUDING OF MERCHANTABILITY, SATISFACTORY
QUALITY AND FITNESS FOR A PARTICULAR PURPOSE.
Please see the CERN OHL v.1.1 for applicable conditions.

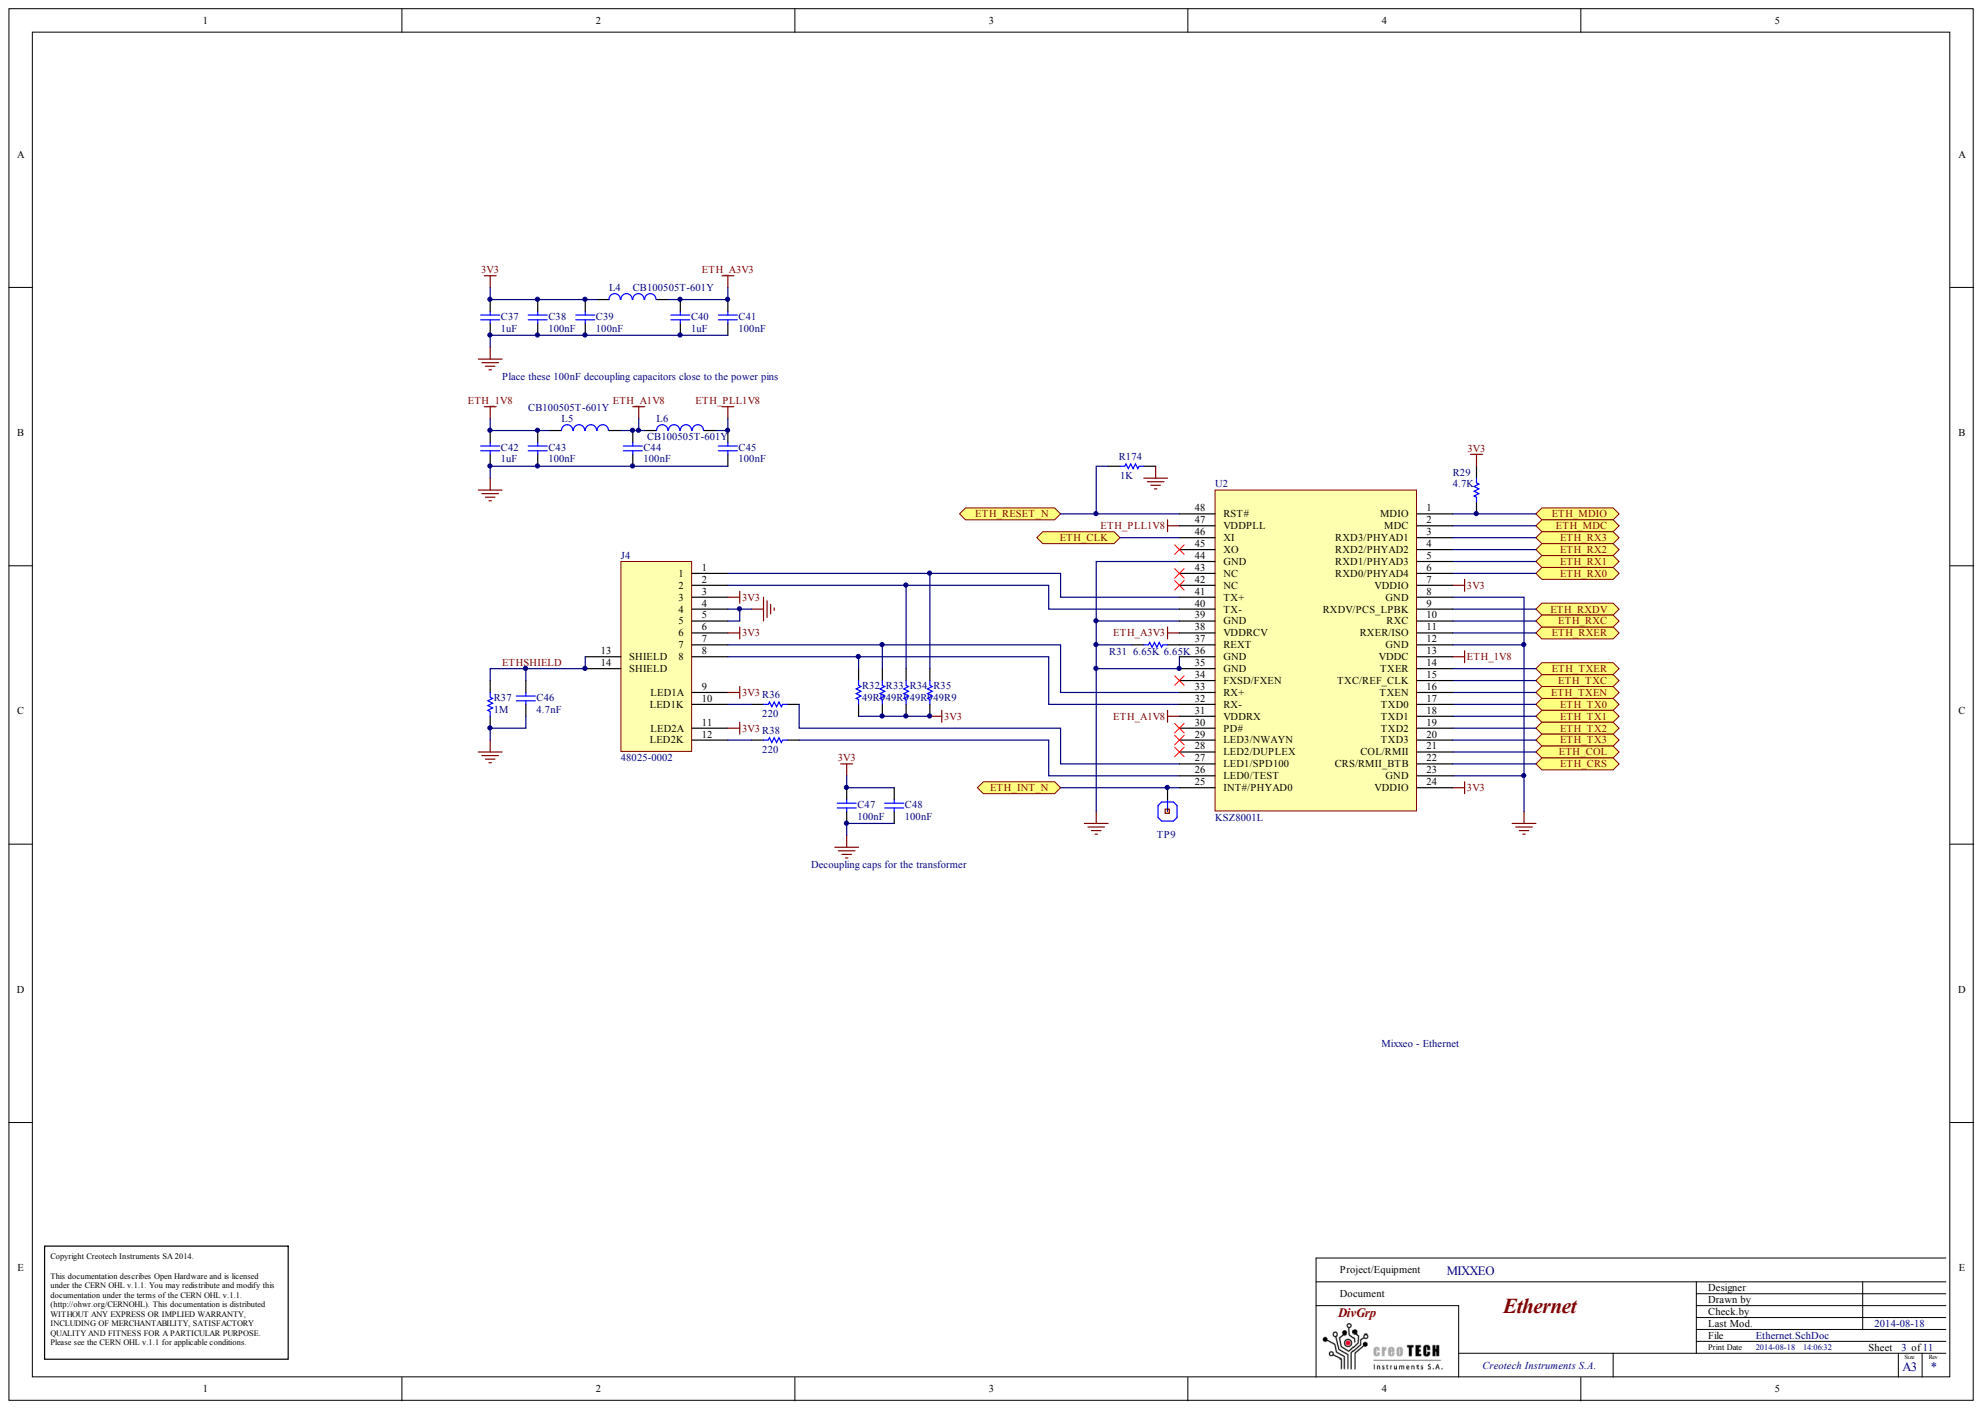
[picture p24: page 2]

Place these 100nF decoupling capacitors close to the power pins

Decoupling caps for the transformer

Copyright Creotech Instruments SA 2014.

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

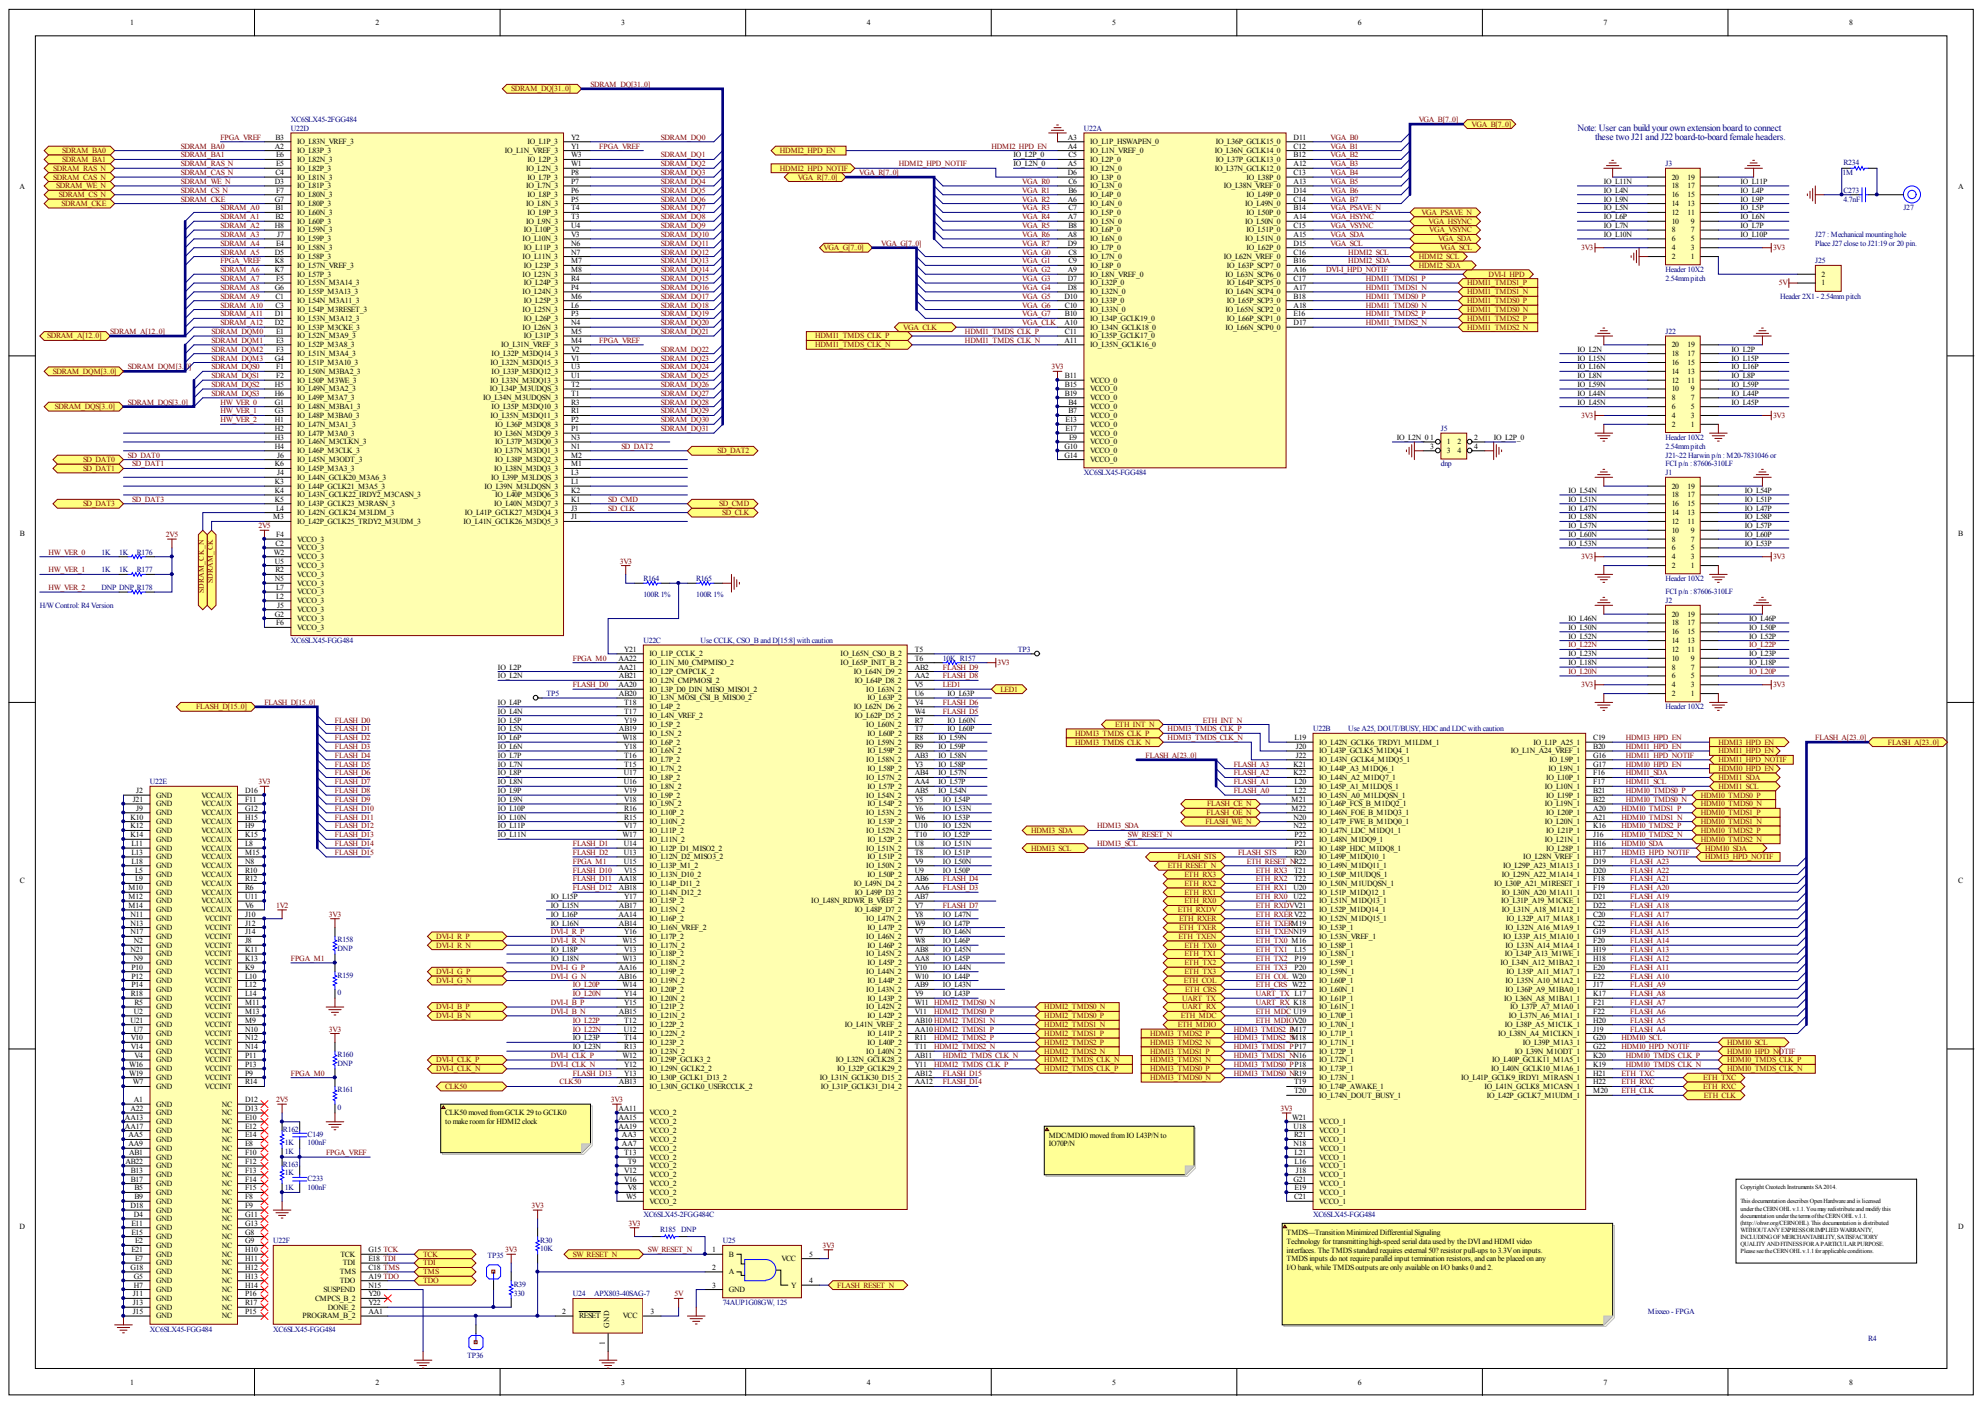
[picture p25: page 3]

Note: User can build your own extension board to connect these two J21 and J22 board-to-board female headers.

J27 : Mechanical mountinghole
Place J27 close to J21:19 or 20 pin.

Use CCLK, CSO_B and D[15:8] with caution

Use A25, DOUT/BUSY, HDC and LDC with caution

CLK50 moved fromGCLK 29 to GCLK0
to make roomfor HDMI2 clock

MDC/MDIO moved fromIO L43P/N to

Copyright Creotech Instruments SA 2014.

This documentation describes Open Hardware and is licensed
undertheCERN OHL v.1.1.You may redistribute and modify this
documentation underthe terms oftheCERN OHL v.1.1.
(http://ohwr.org/CERNOHL).This documentation is distributed
WITHOUTANY EXPRESSORIMPLIEDWARRANTY,
INCLUDING OFMERCHANTABILITY,SATISFACTORY
QUALITY AND FITNESSFORA PARTICULARPURPOSE.
Please see theCERN OHL v.1.1 for applicable conditions.

TMDS—Transition Minimized Differential Signaling
Technology for transmittinghigh-speed serial data used by the DVI and HDMI video
interfaces. The TMDSstandard requires external 50? resistor pull-ups to 3.3Von inputs.
TMDSinputs do not require parallel input termination resistors, and can be placed on any
I/O bank, while TMDSoutputs are only available on I/O banks 0 and 2.

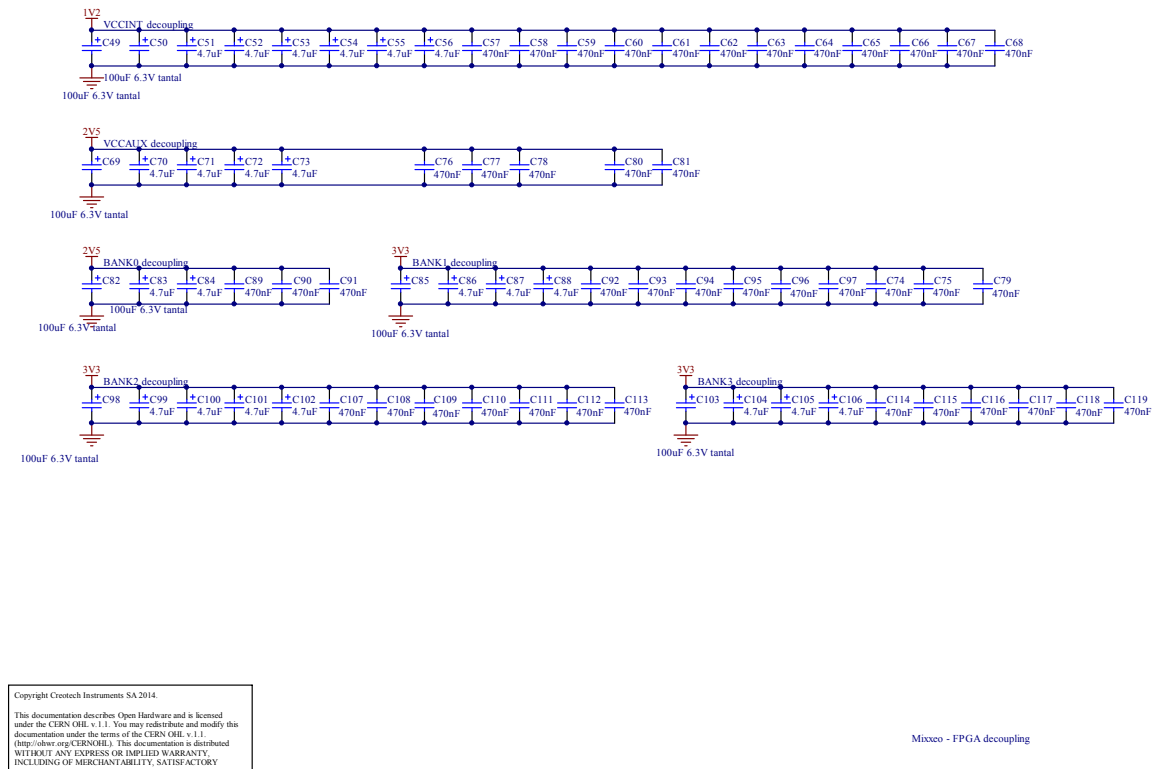
[picture p26: page 4]

Copyright Creotech Instruments SA 2014.

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

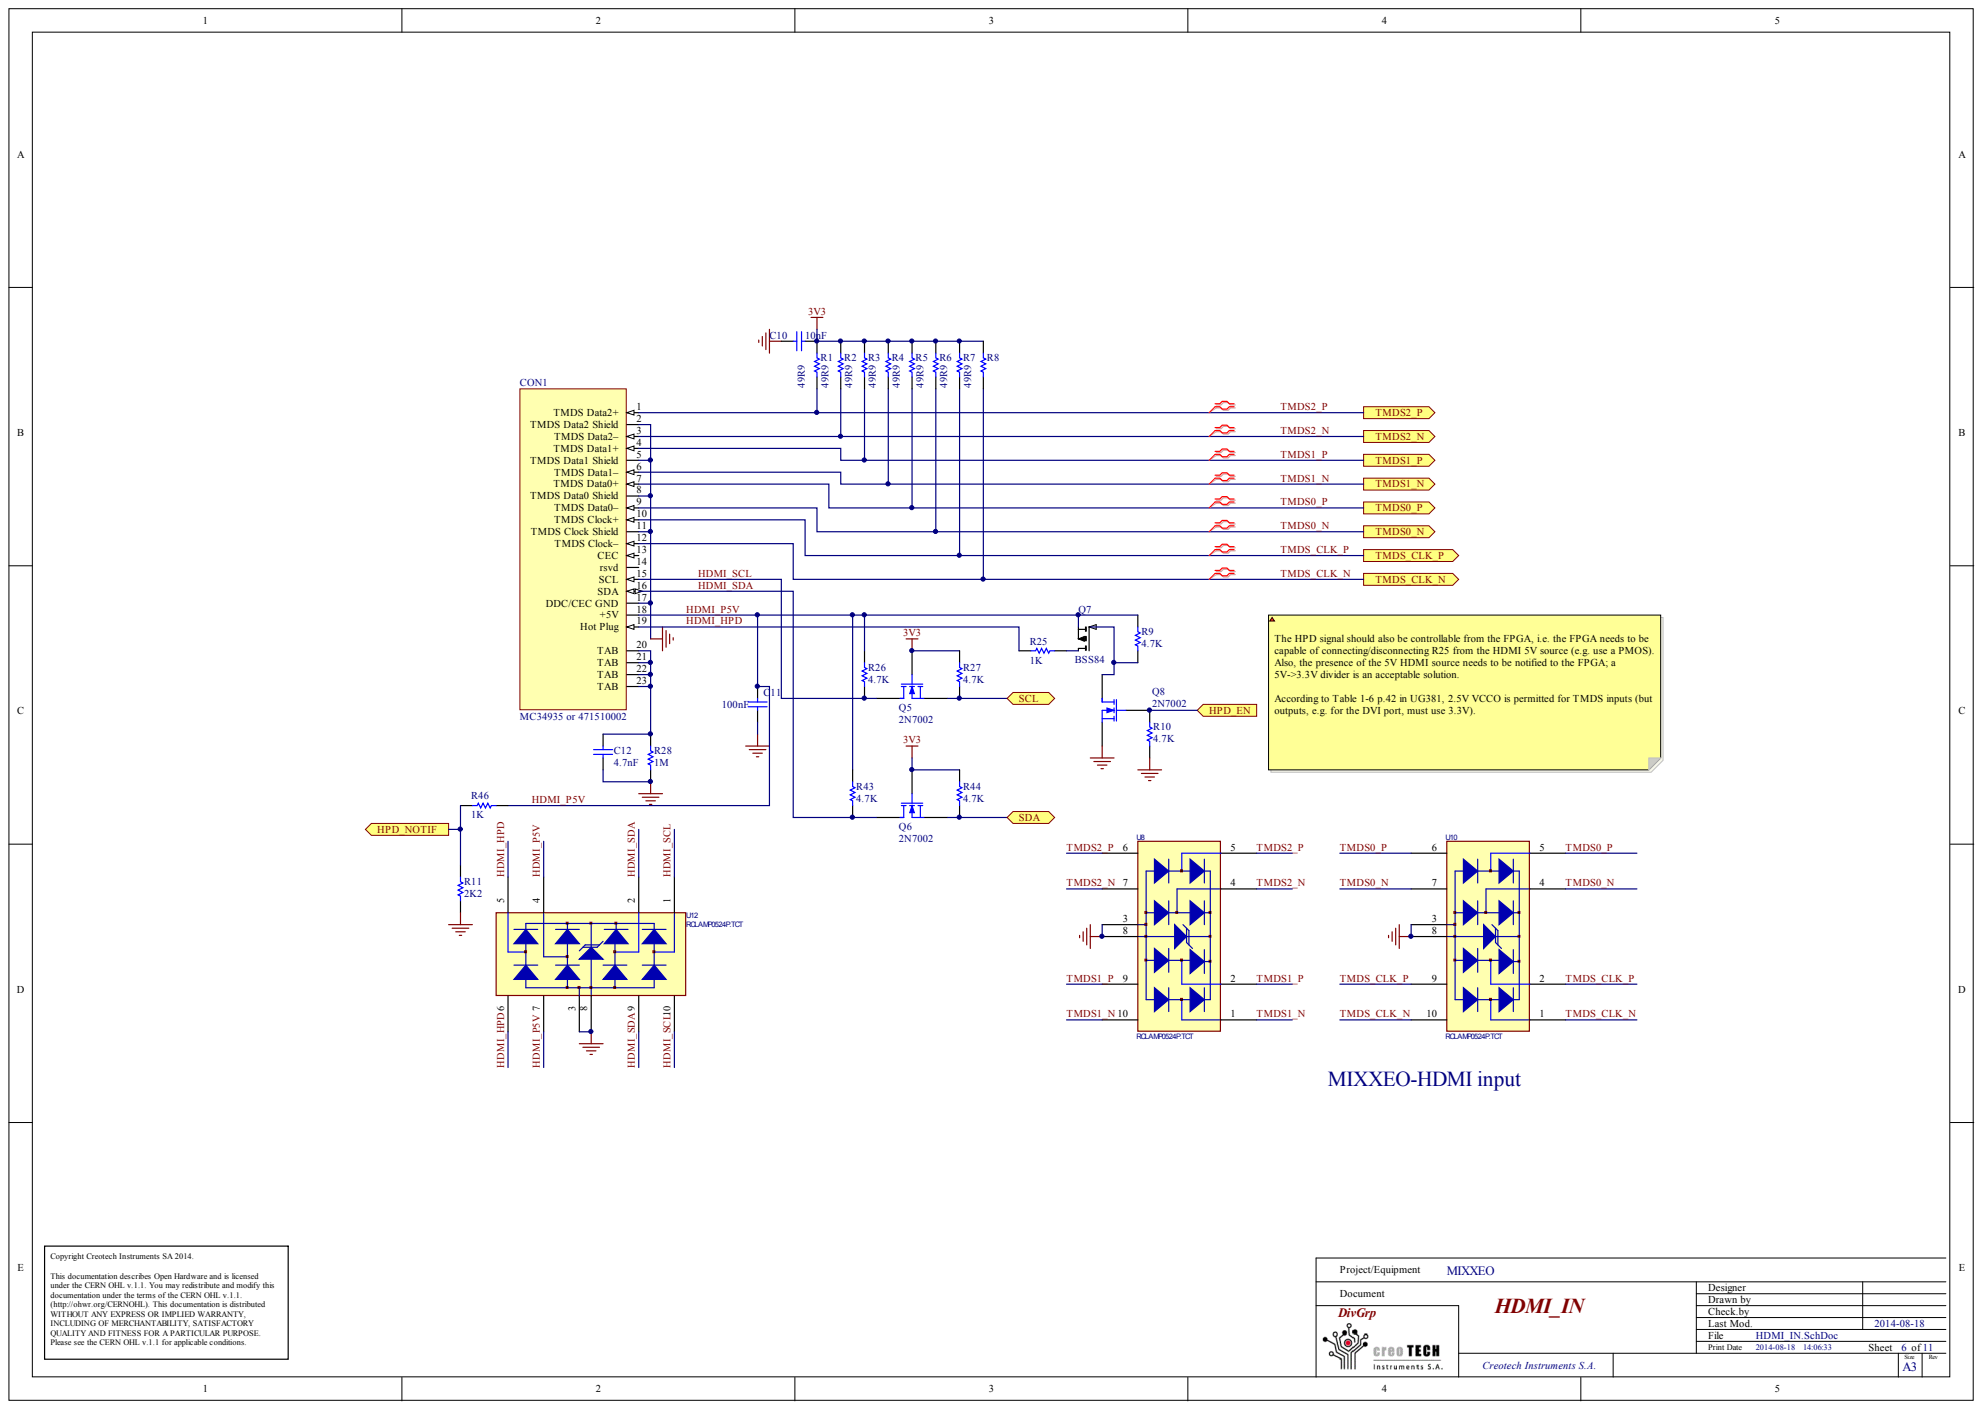
[picture p27: page 5]

The HPD signal should also be controllable from the FPGA, i.e. the FPGA needs to be
capable of connecting/disconnecting R25 from the HDMI 5V source (e.g. use a PMOS).
Also, the presence of the 5V HDMI source needs to be notified to the FPGA; a
5V->3.3V divider is an acceptable solution.

According to Table 1-6 p.42 in UG381, 2.5V VCCO is permitted for TMDS inputs (but
outputs, e.g. for the DVI port, must use 3.3V).

Copyright Creotech Instruments SA 2014.

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

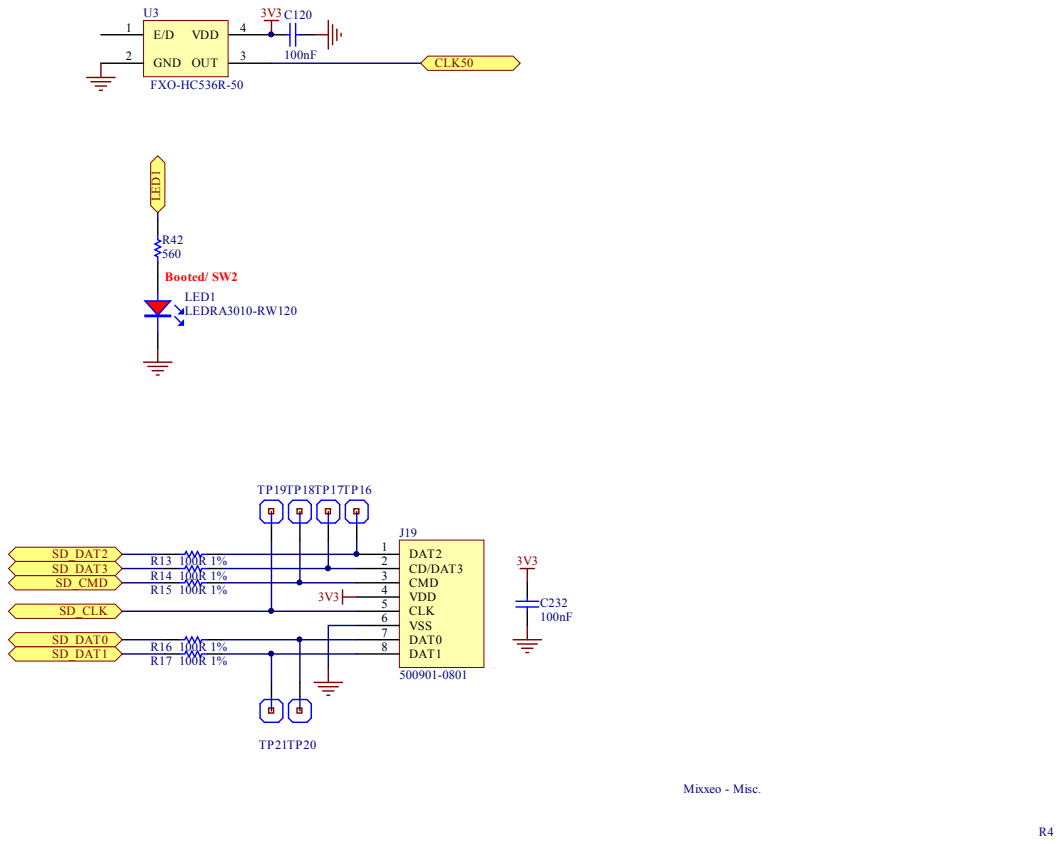
[picture p28: page 6]

Copyright Creotech Instruments SA 2014.

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

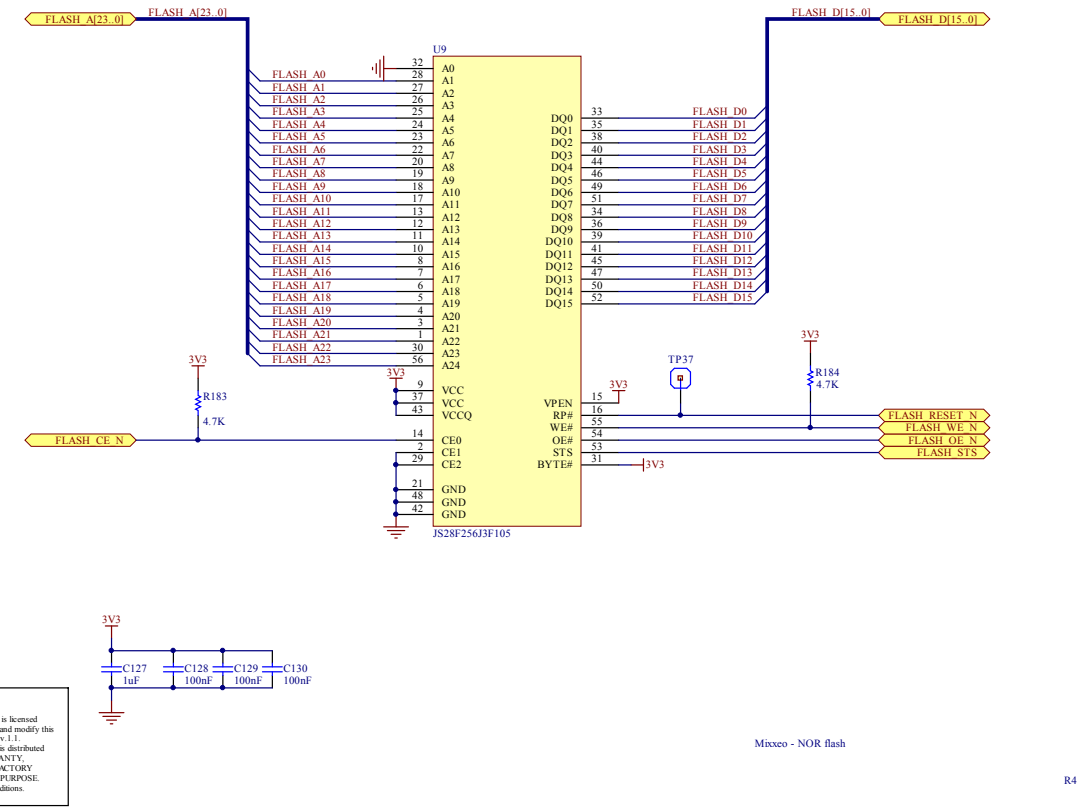
[picture p29: page 7]

Copyright Creotech Instruments SA 2014.

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

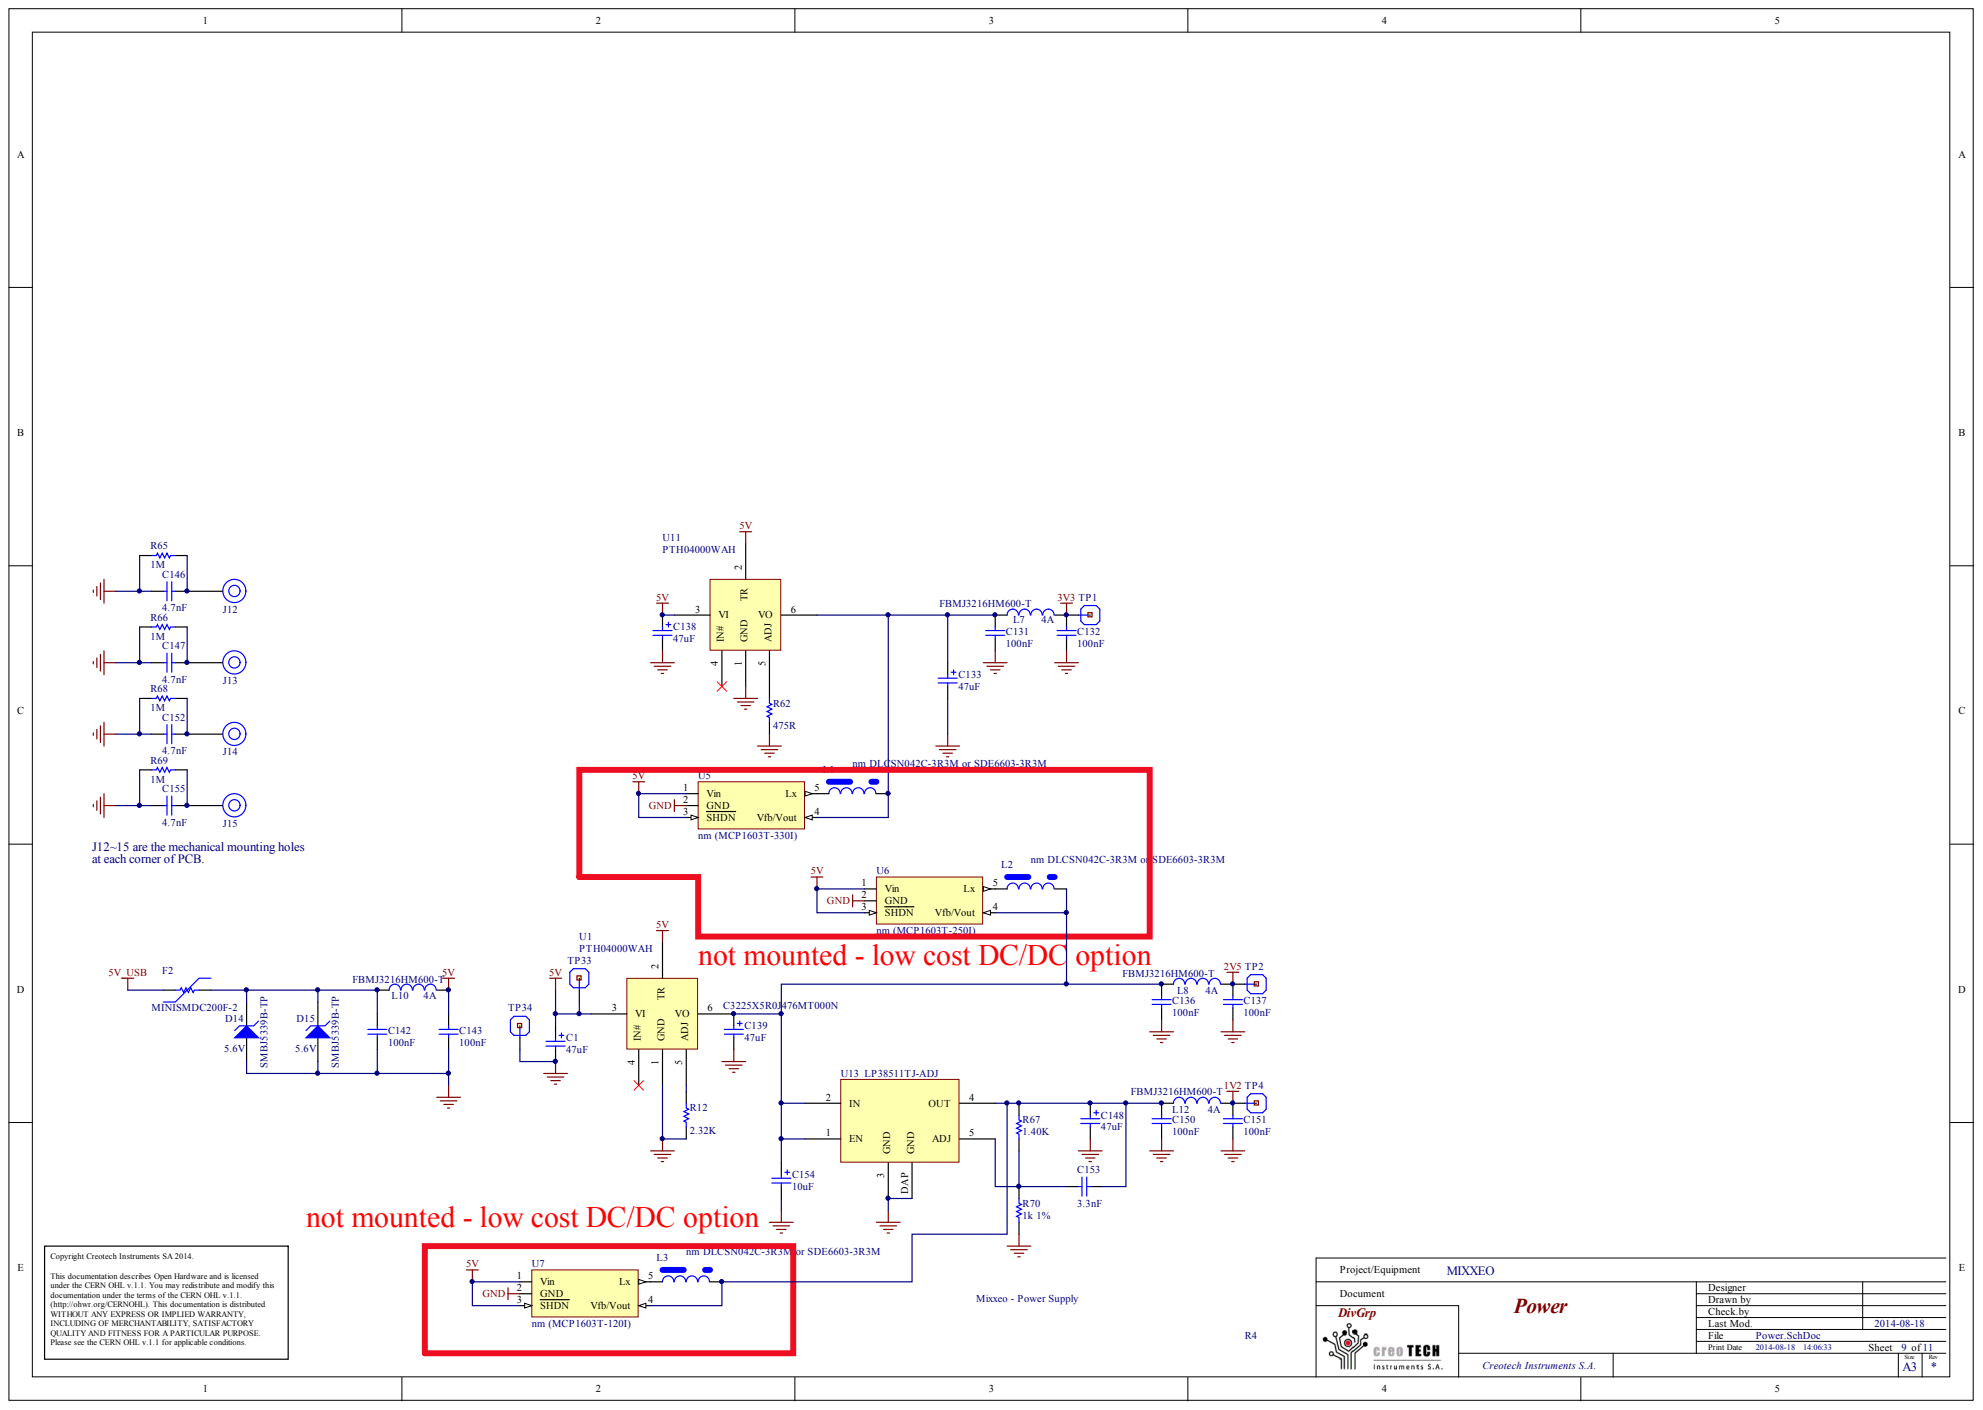
[picture p30: page 8]

J12~15 are the mechanical mounting holes at each corner of PCB.

not mounted - low cost DC/DC option

Copyright Creotech Instruments SA 2014.

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

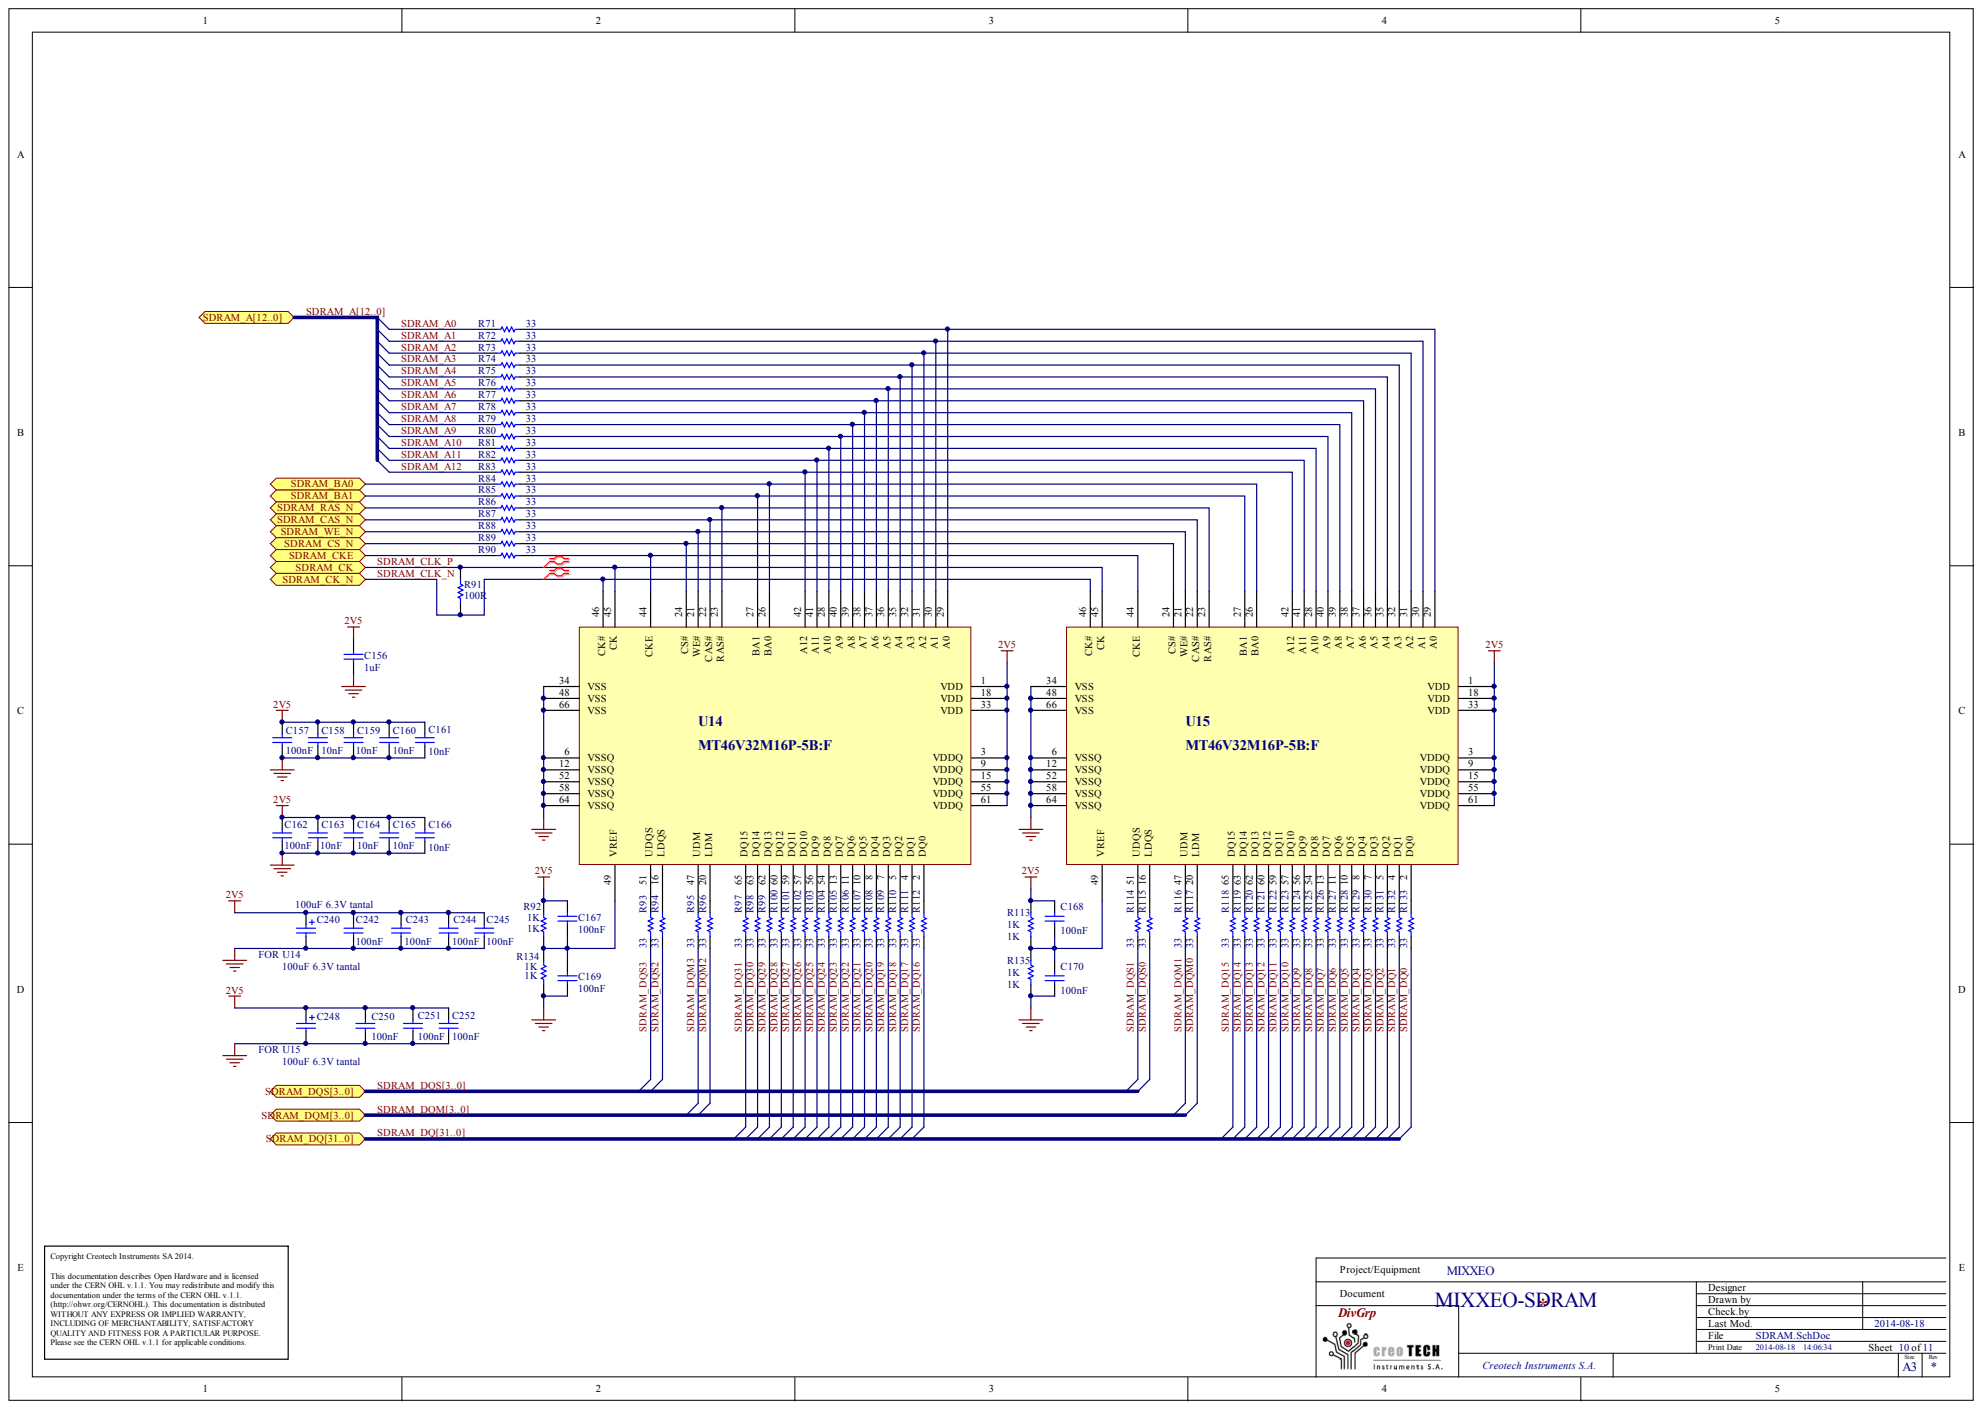
[picture p31: page 9]

Copyright Creotech Instruments SA 2014.

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

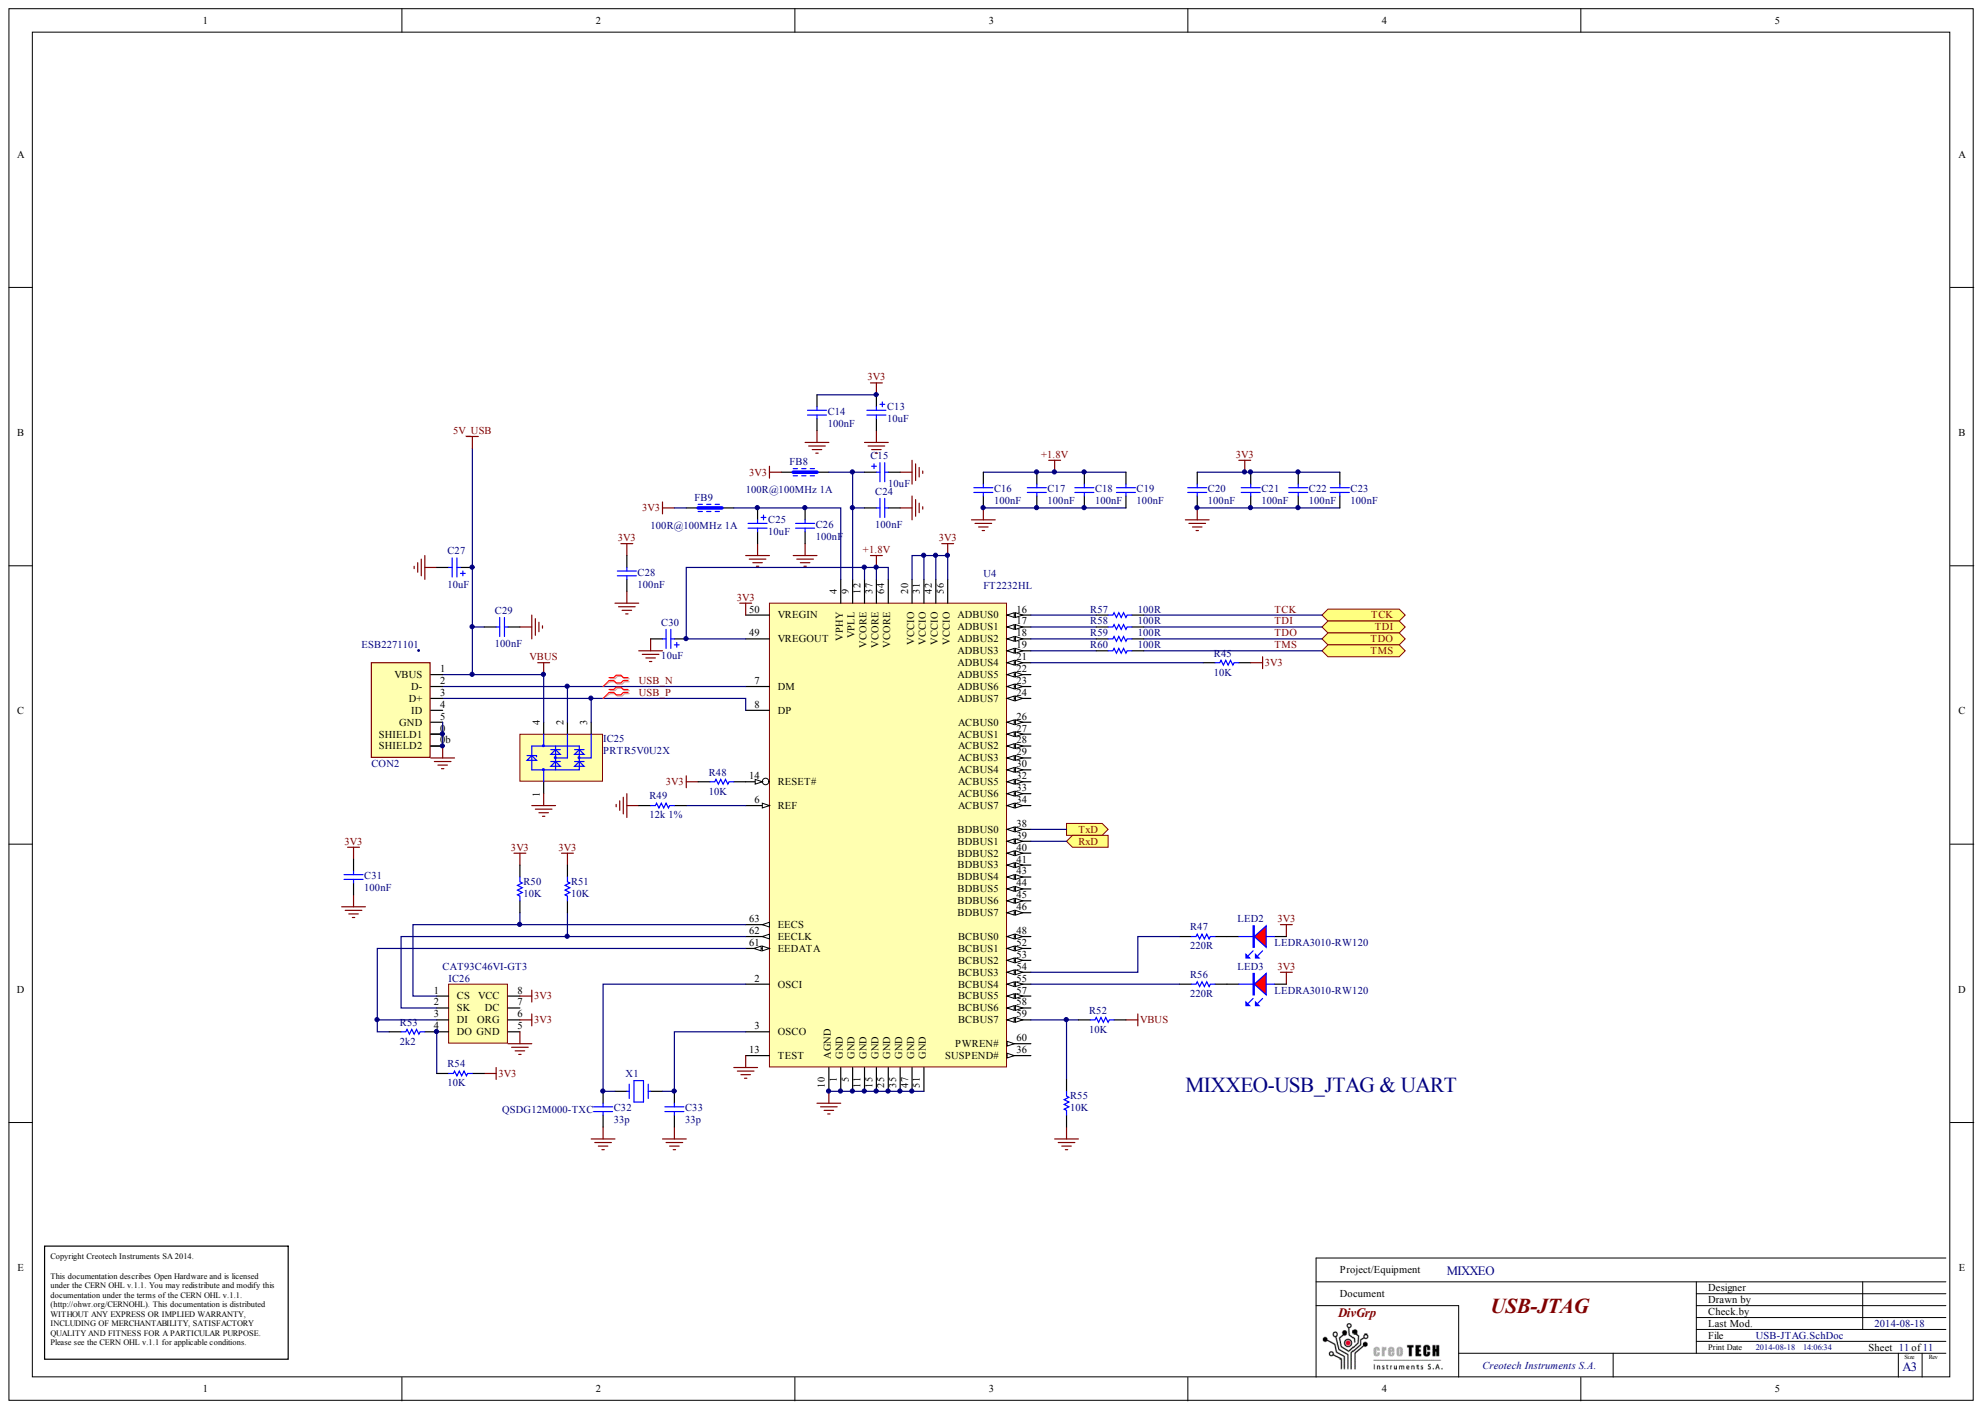
[picture p32: page 10]

EECLK 62
EEDATA 61

CAT93C46VI-GT3 IC26 | | OSCI 2

SK 2
DI 3

Copyright Creotech Instruments SA 2014.

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

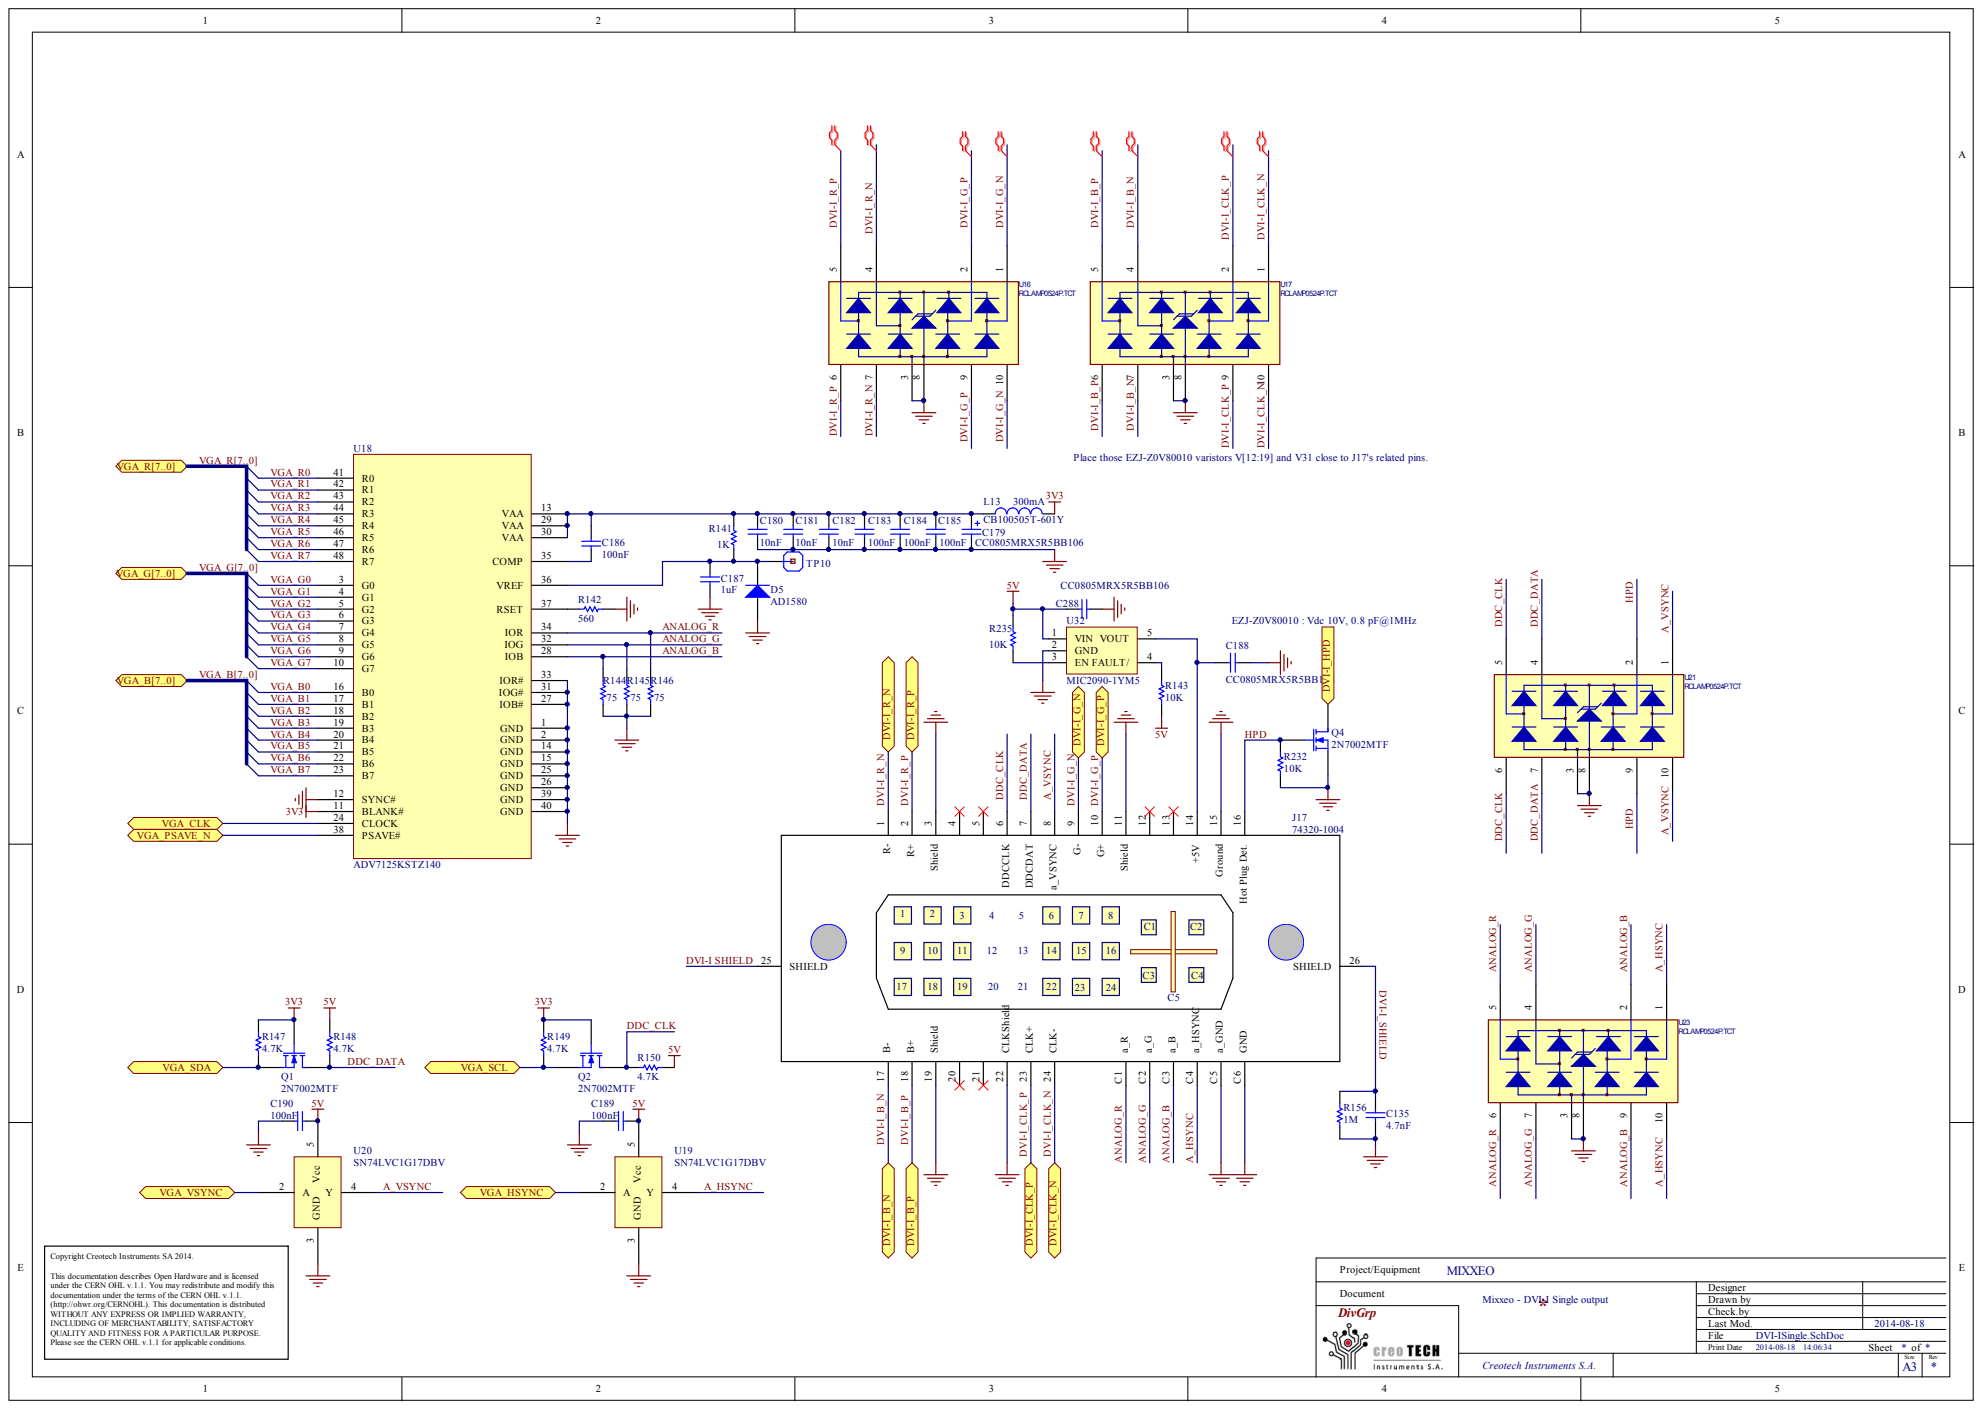
[picture p33: page 11]
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
