knivd/Configum1/docs/Spartan 6/Examples/usb-fpga-2.04.pdf

# Circuit diagram of ZTEX USB-FPGA-Module 2.04

Contents:
Sheet 1 | EZ-USB FX2, USB, EEPROM
Sheet 2 | JTAG, SPI Flash, XC6S Banks 1 and 2 (FX2 - FPGA interface, external I/O rows C and D)
Sheet 3 | XC6S Bank 0 (external I/O rows A and B)
Sheet 4 | DDR SDRAM (XC6S Bank 3)
Sheet 5 | IC power supply, Decoupling
Sheet 6 | Voltage regulators

http://www.ztex.de

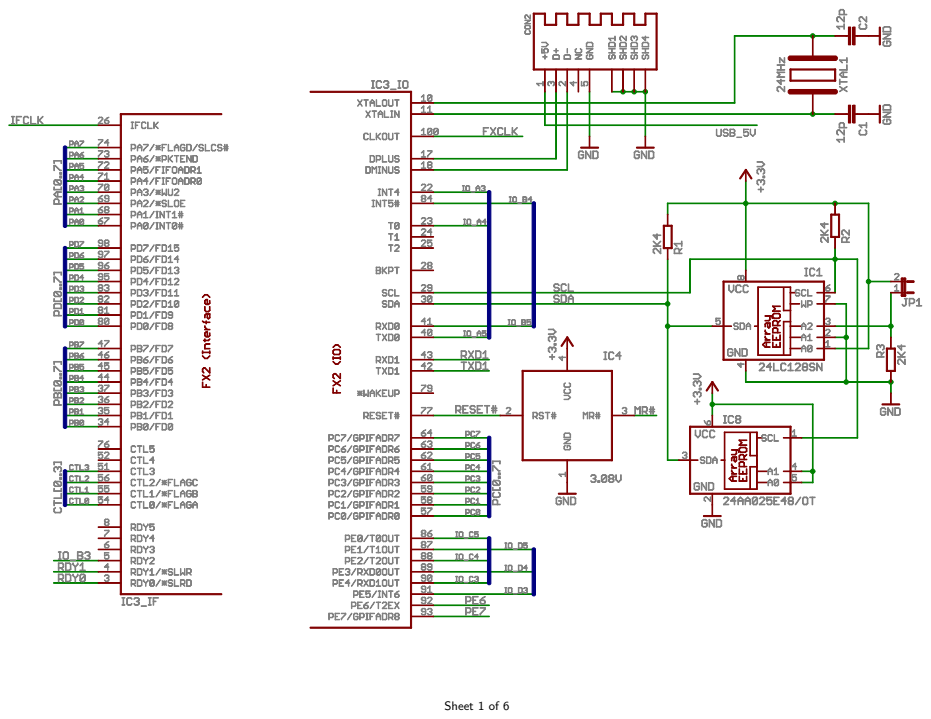
[picture p34: page 2]
Sheet 1 of 6

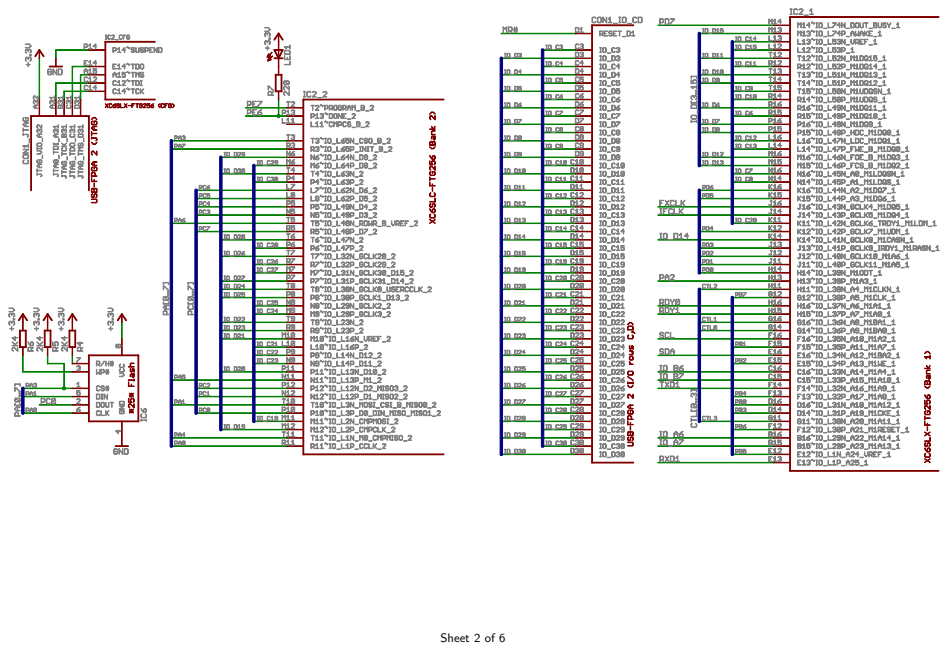
[picture p35: page 3]

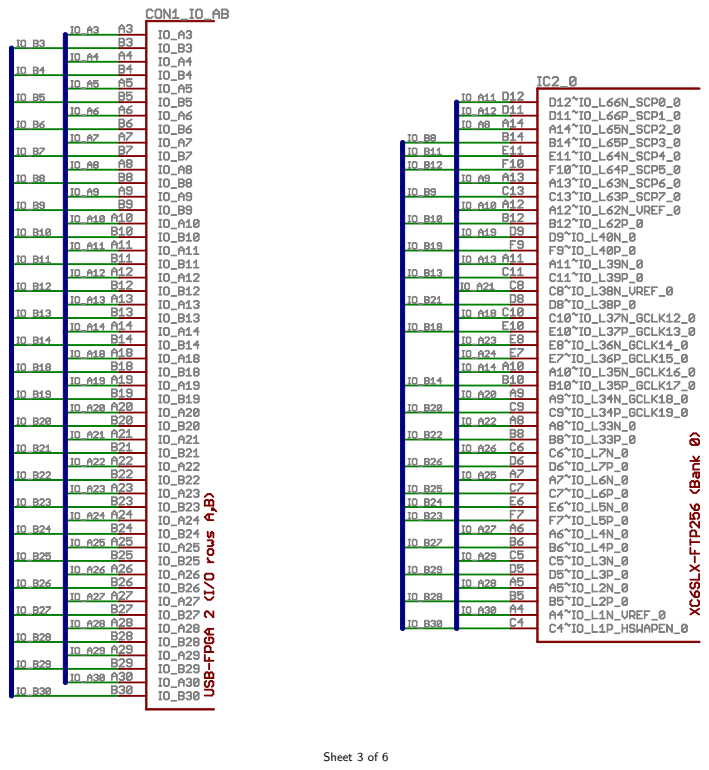
[picture p36: page 4]

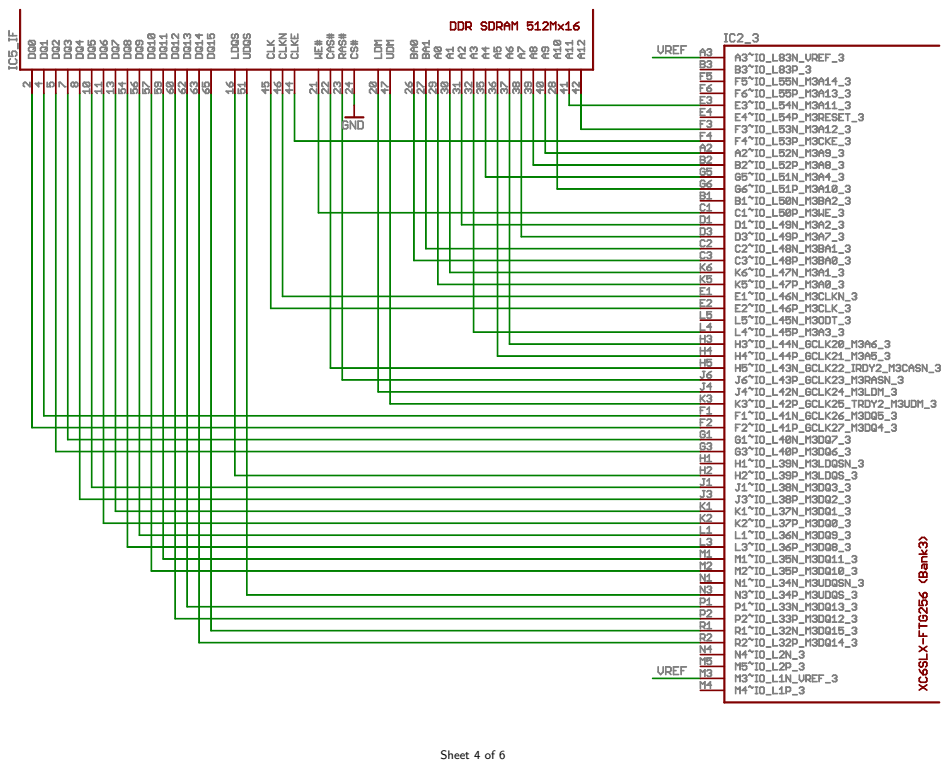
[picture p37: page 5]

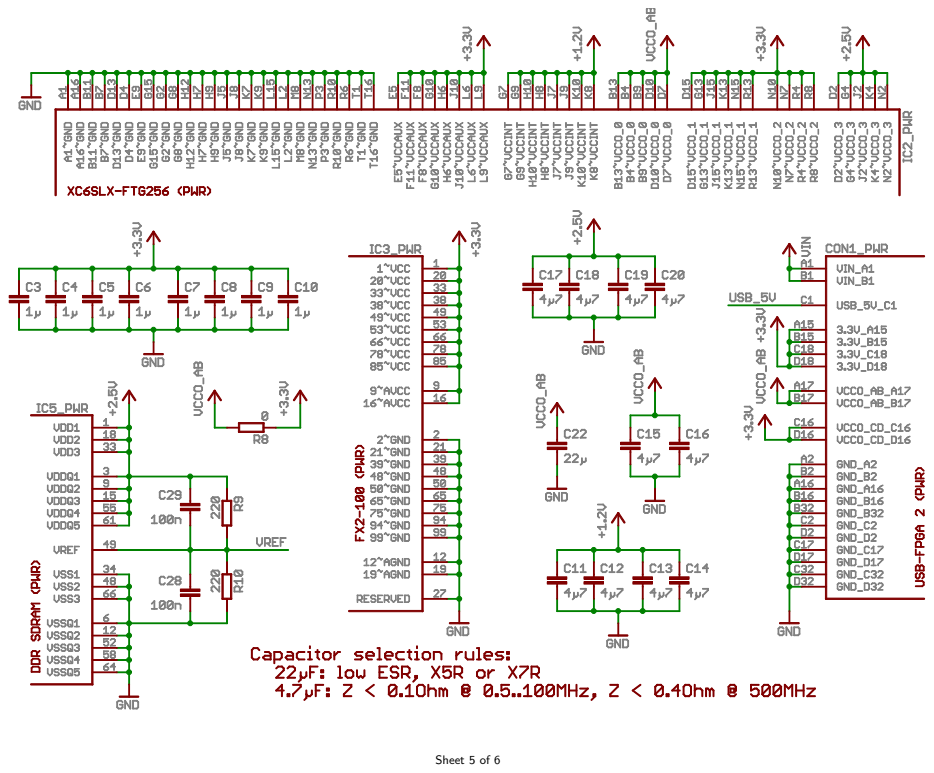
[picture p38: page 6]

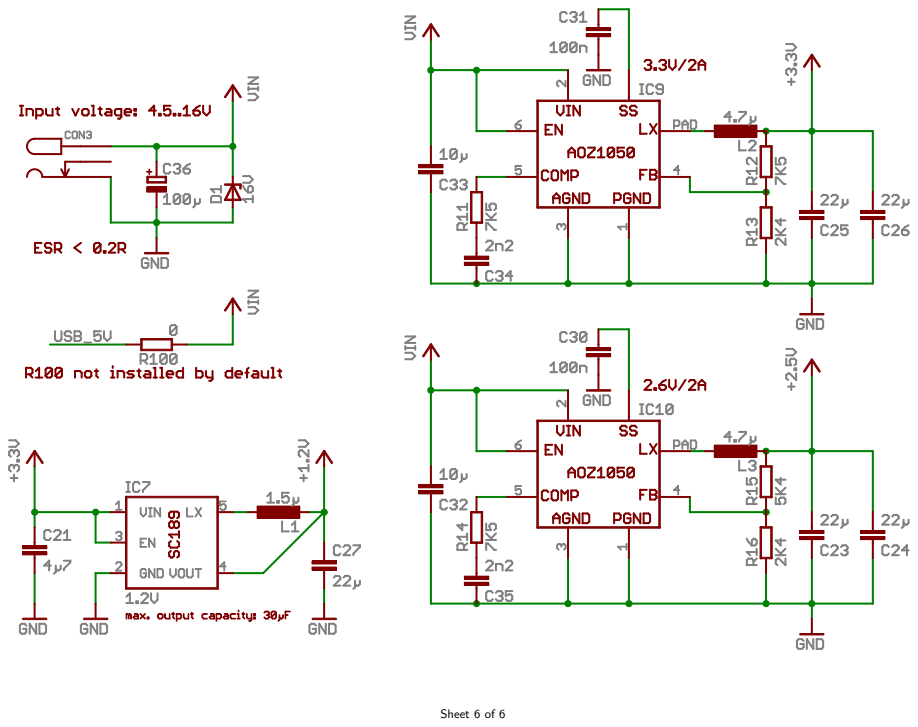
[picture p39: page 7]
